kvderevyanko/klicad/hardware/evidence/rev1-preproduction-silkscreen-implementation-2026-08-21/implementation-handoff.md

# Rev.1 pre-production silkscreen implementation handoff

## SCOPE STATUS

`IMPLEMENTED — INDEPENDENT IMPLEMENTATION REVIEW REQUIRED`

The active board now exactly matches the independently reviewed candidate
`hardware/evidence/rev1-preproduction-silkscreen-plan-2026-08-21/20-silkscreen-candidate-b.kicad_pcb`.

## Transaction

- Pre-transaction active SHA-256: `fa4bfbc0db8a9b99583374f5a4f6836f2e5478efc125d0bf91d148ff16ddc1be`.
- Named backup: `01-active-pre-silkscreen-fa4bfbc0.kicad_pcb`.
- Final active SHA-256: `a9fa9493ec7dfbc3f0cfb2c761cb3d6d895543bd6ade34848f83fb86fcffec0c`.
- Final active board is byte-identical to reviewed candidate B (`cmp` PASS and equal SHA-256).
- Exactly 34 board-level `F.SilkS` text objects were added: board `gr_text` count changed from 12 to 46.
- Existing title block and retained Dwgs.User status text were preserved byte-for-byte from the transaction baseline.
- No footprint graphics, footprint origin/rotation, track, via, zone, rule-area, or Edge.Cuts item was changed.

## Critical geometry

All text centres, rotations, sizes, and strokes are exactly those in
`silkscreen-physical-plan.md`. Every new label is at least 0.80 mm high with
0.15-mm stroke; the four high-level orientation labels are 0.90 or 1.00 mm
high. J3 `PIN 1 / M0` remains unchanged.

## Machine gates

- Pre-transaction protected fast contract: PASS.
- Post-transaction protected fast contract: PASS.
- Native KiCad DRC with `--severity-all`: 0 violations, 0 unconnected items.
- Schematic/PCB parity: PASS; 37 PCB footprints and two intentional no-footprint DNP items.
- Full board contract: PASS; 37 footprints, 200 tracks, 58 vias, four zones, two copper layers, 145 x 90 mm.
- Normalized immutability: PASS. The accepted candidate comparison fingerprint is unchanged before/after (`c198408a...c761`); footprint placement/pads, segments, vias, copper zones and fills, antenna keepout, connectivity, and Edge.Cuts are identical.

## Delta and preservation

- Expected DRC delta: none. Observed DRC delta: none.
- Expected copper/placement delta: none. Observed copper/placement delta: none.
- Retained: prior title-block cleanup, prior Dwgs.User cleanup, all completed routing, U3 DBV release, U4 thermal geometry, antenna exclusion, and all footprint positions.
- Deferred: none within this approved transaction.
- Failed: none.

## Next gate

Independent `pcb_reviewer` implementation review. This handoff is a process
status and is not approval.

Evidence: `00-pre-fast-contract.log`, named backup `01-*`,
`02-post-fast-contract.log`, `03-post-drc.json`, `04-post-parity.json`,
`05-post-full-contract.log`, `06-normalized-geometry-delta.json`, and
`07-sha256.log`.
