kvderevyanko/klicad/hardware/evidence/agent-refactor-2026-08-20/agent-context.md

# Active agent context — ESP32 + E220 carrier Rev.1

Audience: `AGENT_FACING`. This is the concise English operational source for agents. Validate mutable geometry and checker counts against the actual files before acting.

## Product boundary

The PCB is a two-layer carrier for a removable 30-pin ESP32 DevKit, one removable EBYTE E220-400T22D or E220-900T22D, and a removable 0.96-inch OLED. The active carrier supply is an externally protected 2S Li-ion pack. Superseded carrier USB-C/TUSB320/eFuse power circuitry must not be restored. The DevKit's own USB-C must remain physically accessible and is subject to the documented Rev.A mutual-use/backfeed constraint.

Factory PCBA installs carrier sockets, battery protection, the TPS62133 power cell, passives, and released carrier circuitry. ESP32 DevKit, E220, and OLED modules are user-installed. R10/R11 are `NO_FOOTPRINT_DNP` OLED pull-up options.

## Rev.1 accessory-power and service policy

`U4` is TI `TLV1117LV33DCYR`, a 5-V-to-3.3-V accessory LDO: U4.3=`5V_SYS`, U4.2/tab=`AUX_3V3`, and U4.1=`GND`. C9 and C10 are the prescribed local 10-uF Murata `GRM21BR61E106KA73` input and output capacitors. The current schematic and the electrical evidence are the controlling records: `hardware/esp32-e220.kicad_sch` (U4/C9/C10) and `hardware/evidence/rev1-expansion-2026-08-20/aux-3v3-electrical-handoff.md`.

`AUX_3V3` has a 300-mA total allocation: OLED at J5 = 100 mA, with J6 and J7 together = 200 mA total, not 200 mA per connector. J5.2, J6.9, J7.2, J7.12, R10.2, and R11.2 are on `AUX_3V3`; R10/R11 remain DNP. `DEVKIT_3V3` is J2.1 only and has no approved external-accessory allocation. Do not power an accessory from `DEVKIT_3V3`.

Normal operation is `POWER_SW ON` with `JP1` closed. For USB service, use `POWER_SW OFF` and `JP1` open when isolation is desired. This does not provide automatic or complete GPIO isolation. With carrier power on, `JP1` open, and the DevKit unpowered, a powered J5/J6/J7 peripheral must not actively drive a GPIO. This is an operating-policy limitation; no extra isolation hardware is authorized in this revision. See the same schematic notes and `aux-3v3-electrical-handoff.md` for the exact statement and U4 thermal/layout constraint.

## Recovered 5V_SYS design allocation

`POWER BUDGET PASS` applies to the recovered simultaneous **project design
allocation**, not to a manufacturer maximum of the unidentified removable
DevKit and not to physical-release approval. The exact ledger is
`500.000 mA` DevKit allocation + `110.000 mA` E220 manufacturer instantaneous
22-dBm maximum + `36.600 mA` unreleased-D2 conservative allocation +
`1.510 mA` U3 static test-condition allocation + `300.100 mA` U4/AUX
allocation convention = `948.210 mA`; 20% engineering margin = `189.642 mA`;
total `5V_SYS` design allocation = `1.137852 A`.

The 100-mA OLED allocation is included once within the 300-mA `AUX_3V3`
allocation; J6/J7 receive the other 200 mA combined. The extra 0.100 mA is
not a claimed U4 loaded-current maximum: TI `TLV1117LV` `SBVS160C`, Rev. C,
states that value as maximum no-load quiescent current. `TPS62133` has a 3.0-A
continuous output rating; this allocation is 37.9284% of it and leaves
1.862148 A continuous-rating headroom. Its 3.6-A minimum static current limit
is specified at VIN=12 V / TA=25°C; it is a separate qualification condition,
not the continuous rating or a 6.0-V guarantee.

At 5.0 V, `Pout=5.689260 W`; at the 85% allocation assumption,
`Pin=6.693247 W`, giving battery current `1.115541 A` / `0.904493 A` /
`0.796815 A` at 6.0 V / 7.4 V / 8.4 V. At the 6.0-V worst allocation, F1
`1812L200/16` retains `0.174459 A` to its 1.29-A 85°C `Ihold`; J4 is 3 A,
Q1 is adequate against its cited 2.6-A at 70°C / VGS=-4.5-V condition, and
the selected J8 JST VH 10-A rating has `8.884459 A` arithmetic difference.
These are design-allocation comparisons; harness, hot-board, ripple, and
transient behavior require prototype validation.

`XFL4020-222MEB` is retained without change. Official Coilcraft
`XFL4020-222ME_` data gives 2.2 uH, 23.50-mOhm maximum DCR, 3.1-A 10%-drop
`Isat`, and 6.0-A 20°C-rise `Irms`. At the DC allocation, its DCR-only loss
is `0.030426 W` and the DC-only gap to 3.1-A `Isat` is `1.962148 A`; peak
inductor current with ripple must be measured or calculated for the actual
board. See `hardware/evidence/rev1-expansion-2026-08-20/5v-sys-budget-ledger.md`.

## Approved electrical topology

Input path:

`BAT_PLUS -> F1 -> BAT_FUSED -> Q1 -> BUCK_IN -> U1 TPS62133 -> 5V_SYS`.

TVS shunt:

`BAT_FUSED -> D3 SMBJ10CA -> GND`.

Q1 DMP3130LQ-7 uses manufacturer pins 1=G, 2=S, 3=D. Approved nets are Q1.1=`Q1_GATE`, Q1.2=`BUCK_IN`, Q1.3=`BAT_FUSED`. Do not infer function from visual pad position.

TPS62133RGT functional map from TI TPS6213x Rev.F Table 6-1:

| Pins | Function | Approved net/intent |
| --- | --- | --- |
| 1, 2, 3 | SW | `BUCK_SW` to L1, short F.Cu only |
| 4 | PG | NC in the approved design |
| 5 | FB | GND for fixed output |
| 6 | AGND | local common ground/EP |
| 7 | FSW | `5V_SYS`, logic-high frequency selection; low-current configuration trace |
| 8 | DEF | GND output selection |
| 9 | SS/TR | `SS_TR` to C4; mandatory short control connection |
| 10 | AVIN | `BUCK_IN` with local C2 bypass |
| 11, 12 | PVIN | `BUCK_IN` with local C1 high-di/dt loop |
| 13 | EN | `BUCK_IN` |
| 14 | VOS | `5V_SYS` Kelvin sense at/near C3 output node, not a power branch |
| 15, 16 | PGND | local common ground/EP |
| EP | exposed pad | GND/thermal connection |

No schematic change is currently required for the TPS62133 cell.

## Module interfaces

E220 mapping: GPIO17/TX2 -> E220 RXD; GPIO16/RX2 <- E220 TXD; GPIO25 -> M0; GPIO26 -> M1; GPIO27 <- AUX. M0/M1 have local 10-kOhm pull-downs. E220 VCC uses local 10-uF + 100-nF decoupling. Preserve SMA access and RF separation.

OLED mapping: J5.1=GND, J5.2=`AUX_3V3`, J5.3=GPIO22/SCL, J5.4=GPIO21/SDA. R10/R11 4.7-kOhm pull-ups to `AUX_3V3` are DNP/no-footprint. OLED final mechanical datum remains unresolved.

WS2812/AHCT: U3 SN74AHCT1G125 is approved. D2 remains `PLACEMENT_CANDIDATE_NOT_RELEASED`; do not production-approve its footprint or route final D2-dependent connections unless explicitly released.

## Mechanical and PCB baseline

Board outline: 145 x 90 mm. Planning stack: two layers, 1-oz outer copper assumption pending fabrication confirmation. ESP32, E220, OLED, and J4 locations are protected from casual movement. Preserve ESP32 antenna keepout, DevKit USB-C access, E220 SMA access, and module-removal clearance.

Planning rules:

* SIGNAL: preferred 0.25 mm, 0.20 mm minimum for tight escape, 0.20 mm clearance, 0.60/0.30-mm via.
* POWER: BAT_PLUS, BAT_FUSED, BUCK_IN, and main 5V_SYS preferred 1.0 mm; justified local 5V_SYS branches may use 0.8 mm.
* BUCK_SW: short local F.Cu, no via, minimum practical copper, 0.70 mm accepted where 0.80 mm violates actual clearance.

## Current physical state

The active board `hardware/esp32-e220.kicad_pcb` is the accepted controlled-routing physical state of record. Its input protection, TPS62133 buck implementation, and post-C3 `5V_SYS` distribution were independently reviewed and accepted as physical checkpoints; this is not a production release or a substitute for the final independent PCB review.

The active board contains the accepted buck and 5V copper, the bounded B.Cu GND plane, and the local F.Cu buck GND zone. Retain the VOS Kelvin connection at the C3 output node and the FSW configuration connection. The completed power endpoints are ESP32 VIN, E220 VCC with C5/C6 bypass, and U3/C7 power. Only D2.1 remains on the `5V_SYS` deferred list because D2 is `PLACEMENT_CANDIDATE_NOT_RELEASED`; no D2-dependent copper is released.

The active PCB contains a **partial, blocked** Rev.1 expansion transaction: J8/JP1/BAT_SENSE/U4/C9/C10 are present and their changed existing-pad parity is applied, but J6/J7 plus all authorized M3/strain-relief holes are not retained. U4/C9/C10 ground returns and AUX_3V3 endpoint completion remain mandatory airwires. This is not physical approval; see `hardware/evidence/rev1-expansion-2026-08-20/physical-handoff.md`. No schematic owner may edit the active board.

Remaining signal, OLED, UART, GPIO, RF-interface, and test-point connections are unrouted. OLED mechanics remain pending. The active board also intentionally retains the deferred input/test-point airwires `/BAT_PLUS` TP1-to-track and `/BUCK_IN` R2.1-to-track-to-TP3; do not claim that all global electrical airwires are gone and do not repair these outside this scope.

Historical candidate facts are retained only as history: `hardware/esp32-e220-assistant-buck-candidate.kicad_pcb` is an unrouted 0-track/0-via/0-zone placement candidate, not routing authority or a reviewer-approved replacement. `hardware/make_assistant_buck_candidate.py` reproduces that separate candidate without overwriting the active board.

## Deferred items

* OLED mechanical datum/final short connector fanout: pending.
* D2 WS2812 footprint remains `PLACEMENT_CANDIDATE_NOT_RELEASED`; D2-dependent routing is pending.
* All non-power signal routing and the final OLED mechanical integration: pending.
* U4 `AUX_3V3` physical footprint verification, thermal copper/vias, accessory connector placement, and all associated PCB parity/DRC work: pending with `pcb_layout_dfm` after electrical review.
* Prototype validation remains required for DevKit burst/startup current, external-device inrush and capacitance, U4 temperature at the authorized load, TPS62133/F1/Q1 transients, and L1 peak current; the `POWER BUDGET PASS` design allocation is not a prototype result.
* The active PCB is not a production release.

## Primary operational files

* `hardware/esp32-e220.kicad_sch` — approved electrical schematic.
* `hardware/esp32-e220.kicad_pcb` — active controlled-routing physical state.
* `hardware/generate_esp32_e220.py` — reproducible schematic source.
* `hardware/generate_stage7_footprints.py` — active footprint-library source.
* `hardware/generate_stage8_placement.py` — pre-routing candidate generator only; requires an explicit non-active `PLACEMENT_OUTPUT` and never overwrites the active board.
* `hardware/make_assistant_buck_candidate.py` — historical feasibility helper for the separate buck candidate.
* `hardware/rework_buck_local.py` — obsolete failed experiment; not routing authority.
* `hardware/route_5v_distribution.py` — accepted completed-stage helper; requires an explicit board path and stops with `STAGE ALREADY APPLIED` before reapplying accepted copper.
* `hardware/esp32-e220.kicad_pcb` — active routed PCB physical state record.
* `hardware/check_schematic_pcb_sync.py` — approved machine sync gate.
* `hardware/esp32-e220-power-routing-report.md` — English detailed routing checkpoint evidence.
* `hardware/esp32-e220.pretty/README.md` — English footprint-library evidence.

## Required validation

Use native KiCad ERC/DRC and the project sync checker. Report DRC geometry separately from expected out-of-scope unconnected items. Never alter connectivity merely to silence a checker; classify representation differences versus real mismatches. Final electrical and physical acceptance belongs only to `pcb_reviewer`.
