kvderevyanko/klicad/hardware/releases/rev1-q1-footprint-correction-2026-09-11/fabrication/DRILL_REPORT.txt

Drill report for esp32-e220.kicad_pcb
Created on 2026-09-11T11:37:57

Copper Layer Stackup:
    =============================================================
    L1 :  F.Cu                      front
    L2 :  B.Cu                      back

Drill file 'esp32-e220-PTH.drl' contains
    plated through holes:
    =============================================================
    T1  0.300mm  0.0118"  (58 holes))
    T2  1.000mm  0.0394"  (20 holes))
    T3  1.040mm  0.0409"  (41 holes))

    Total plated holes count 119

Drill file 'esp32-e220-NPTH.drl' contains
    unplated through holes:
    =============================================================
    T1  3.200mm  0.1260"  (3 holes))

    Total unplated holes count 3
