kvderevyanko/klicad/docs/open-questions.md

# Вопросы первой статьи Rev.1

Электрическая архитектура, размещение, трассировка и возвратные пути Rev.1 завершены. Этот список не разрешает изменение платы без отдельной согласованной стадии.

## OLED

Розетка J5 и её электрические цепи завершены. Конкретный OLED остаётся механическим риском первой статьи: подтвердить габариты корпуса, высоту, отверстия, доступность разъёма и зазоры. Не вводить на фабричном шелкографии непроверенный точный контур дисплея.

## Корпус и жгут

- Крепёж платы: **отложен до корпуса / Rev.2**. На Rev.1 не добавлять произвольные монтажные отверстия без датумов корпуса.
- Разгрузка аккумуляторного кабеля: **ответственность корпуса / жгута в Rev.1**.
- Проверить доступ к J4, J8, JP1, USB-C ESP32, SMA E220, J5, J6, J9 и TP1…TP5 с реальными разъёмами и инструментом.

## Проверки первого образца

- переходные процессы батареи, F1/D3/Q1 и TPS62133;
- температура U1, L1, Q1, F1, D3 и U4 при OLED-нагрузке;
- фактический ток OLED и внешней цепи до трёх WS2812B-V5;
- работа E220 с согласованной 400- или 900-МГц антенной;
- сопряжение розеток с фактическими ESP32 DevKit, E220 и OLED;
- кнопки J6 и пользовательский RGB J9;
- технологические возможности сборщика для EP U1, U4 SOT-223 и DBV U3.

## Политика выпуска

Rev.1 имеет завершённую связность, но пока не является производственным выпуском. Gerber, сверловка, производственный BOM и CPL создаются только отдельной задачей после финального предсерийного ревью.
