kvderevyanko/klicad/hardware/evidence/preexisting-esp32-e220-artifacts/esp32-e220-gate.pdf

1 | 2 | 3 | 4 | 5 | 6
1 | 2 | 3 | 4 | 5 | 6

AB

C

D

AB

C

D Date:

Size: A4 | Rev:
KiCad E.D.A. 10.0.5 | Id: 1/1

## Title: ESP32 E220 LoRa Receiver — Stage 5 modular carrier

File: esp32-e220.kicad_sch

Sheet: /

2 R5

2 C1

# #FLG02 PWR_FLAG

# #FLG01 PWR_FLAG

# 2 D1 MMSD4148T1G

2 R7

2 C3

1

2

3

4

5

6

7

8 U2

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
15 | J1 DEVKIT_LEFT (USB-C | toward antenna)

2 R6

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
15 | J2 DEVKIT_RIGHT (USB-C | toward antenna) A1

A4

A5

A6

A7

A8

A9

## A12 B1B4B5B6B7B8B9 B12

SH1

# SH2 J4 USB4105-GF-A

1

2

3

4

5

6

7 J3

E220-T22D SOCKET — | FIT | 400T22D OR 900T22D

1

2 C6 GRM188R71C104KA01D 100nF 16V X7R

1

2 C5 GRM188R61A106MAAL 10uF 10V X5R

1

2 R8

10k 1% M0 reset pull-down

1

2 R9

10k 1% M1 reset pull-down

1

2

3

4

5 U3

SN74AHCT1G125DBVR

1

2 C7 GRM188R71C104KA01D 100nF 16V X7R

2 R1

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
12 U1

# #FLG03 PWR_FLAG 1

OLED_SDA OLED_SCL CC2

VBUS_DET USB_DP_NC

E220_RXD USB_DM_NC

CC1

E220_TXD

E220_M0
E220_M1
E220_RXD

E220_M0

VBUS_PRE GND

GND

VBUS_PRE USB_DP_NC

CC1

VBUS_PRE GND

E220_TXD WS2812_DATA_3V3 GND

5V_SYS

TUSB_VDD

5V_SYS

# 5V_SYS GND

WS2812_DATA_3V3 GND WS2812_DIN

GND

GND

# 5V_SYS GND

5V_SYS

E220_AUX

5V_SYS GND

E220_M0 | E220_M1 CC2 GND
GND | GND OVLO

OUT1

5V_SYS GND

DVDT EFUSE_EN

GND

# 5V_SYS USB_DM_NC

VBUS_PRE

VBUS_PRE GND

GND

GND | QBASE

# VBUS_PRE GND

TUSB_VDD

E220_M1

# E220_AUX GND QBASE

GND

5V_SYS

ILM
OVLO

TUSB320 UFP/GPIO: PORT=GND, ADDR=NC, EN_N=GND. OUT1/Q1 gates TPS259630: Default/detach OFF; Medium/High ON.

GPIO4 -> SN74AHCT1G125DBVR (OE=GND, | 5V) | -> WS2812B-V5 DIN. No WS2812 footprint assigned at schematic stage.

USB4105-GF-A: all A/B VBUS, GND and shell contacts are explicit; D+/D- are local NC nets, SBU pins NC, no ESP USB connection.

Stage 5 — main board only. DevKit USB-C programming and main-board USB-C power are mutually exclusive (approved Rev A policy).

No bare ESP32, 3V3 buck, EN/BOOT or programming circuit on this PCB. J1/J2 are the verified removable DevKit sockets.

J3 is universal E220-T22D interface: fit one E220-400T22D OR E220-900T22D. No socket/footprint is selected.

E220 M0/M1 use 10k pull-downs to GND (PROJECT DESIGN CHOICE): reset mode M1/M0=00. AUX is input-only, no pull-down.

OLED: GPIO21/SDA and GPIO22/SCL are signal-only reservations; OLED VCC and I2C pull-ups are NC/DNP in Rev A.

2 U1

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
12 #FLG03 PWR_FLAG

R1

2 C1

# 2 #FLG02 PWR_FLAG #FLG01 PWR_FLAG

# D1 MMSD4148T1G

2 R5

2 | R6

J3

E220-T22D SOCKET — | FIT | 400T22D OR 900T22D

1

2

3

4

5

6
7 | C6 GRM188R71C104KA01D 100nF 16V X7R

1

2 C5 GRM188R61A106MAAL 10uF 10V X5R

1

2 | R8

10k 1% M0 reset pull-down

1

2 | R9

10k 1% M1 reset pull-down

1

2 | U3

SN74AHCT1G125DBVR

1

2

3

4
5 | C7 GRM188R71C104KA01D 100nF 16V X7R

1

2
