kvderevyanko/klicad/hardware/evidence/preexisting-esp32-e220-artifacts/esp32-e220-oled-final.pdf

1 | 2 | 3 | 4 | 5 | 6
1 | 2 | 3 | 4 | 5 | 6

AB

C

D

AB

C

File: | esp32-e220.kicad_sch | D Date:
| | | DEVKIT_3V3 GND
KiCad E.D.A. 10.0.5 | Id: 1/1
Size: | A4 | Rev:

## Title: ESP32 E220 LoRa Receiver — Rev.1 protected 2S battery carrier

Sheet: / | 1

# TP2 GND

TP7

E220_M1

1

2 R9

10k 1% M1 reset pull-down

1

2 R1

100k 1% (Q1 gate pull-down) 1

2 D3

SMBJ10CA (bidirectional TVS) 1

2 R2

1M 1% (Q1 gate-source)

# #FLG04 PWR_FLAG

# #FLG03 PWR_FLAG

1

2

3

4

5 U3

SN74AHCT1G125DBVR

# #FLG05 PWR_FLAG

1

2 F1

1812L200/16 (2A hold PPTC) | TP8

E220_AUX

1

2 J4 PROTECTED 2S LI-ION INPUT ONLY 6...8.4V

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
EP | U1
TPS62133RGT | (5V | / 3A BUCK) 1

2

3 Q1 DMP3130LQ-7 | (reverse-polarity) | 1

2 C4 GRM1885C1H332JA01D 3.3nF 50V C0G (SS/TR)

# #FLG02 PWR_FLAG

# #FLG01 PWR_FLAG

1

2 C2 GRM188R71C104KA01D 100nF 16V X7R (AVIN) 1

2 C1 GRM21BR61E106KA73 10uF 25V X5R (BUCK IN)

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
15 | J1 DEVKIT_LEFT (USB-C | toward antenna) | 1

2

3

4

5

6

7 J3

E220-T22D SOCKET — | FIT | 400T22D OR 900T22D

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
15 | J2 DEVKIT_RIGHT | (USB-C | toward antenna) | TP3 BUCK_IN

1

2 L1

XFL4020-222MEB 2.2uH

1

2 C6 GRM188R71C104KA01D 100nF 16V X7R

TP1 BAT_PLUS

TP6

E220_M0

1

2 C7 GRM188R71C104KA01D 100nF 16V X7R

1

2 R8

10k 1% M0 reset pull-down

TP9

E220_RXD

E220_VCC

E220_TXD

TP4

5V_SYS

1

2 R10 DNP 4.7k 1% OLED SDA pull-up to 3V3

1

2 C5 GRM188R61A106MAAL 10uF 10V X5R

1

2 C3 GRM21BR61A226ME44 22uF 10V X5R (BUCK OUT) BUCK_IN

BUCK_IN

GND

BUCK_IN

SS_TR

BUCK_IN

GND

GND

5V_SYS

5V_SYS

E220_AUX BUCK_IN

BUCK_IN
GND
BUCK_IN | SS_TR

GND

BUCK_SW

BUCK_SW

BUCK_SW

WS2812_DATA_3V3 DEVKIT_3V3 | BUCK_IN
Q1_GATE | OLED_SDA OLED_SDA 5V_SYS DEVKIT_3V3
E220_RXD | WS2812_DIN

5V_SYS WS2812_DATA_3V3 GND

GND WS2812_DIN

OLED_SCL 5V_SYS | OLED_SCL DEVKIT_3V3
5V_SYS | GND

GND

GND

GND
GND

5V_SYS BUCK_IN

E220_M1 GND

GND

E220_M1 Q1_GATE | BUCK_IN
GND | Q1_GATE DEVKIT_3V3 | BAT_PLUS BAT_PLUS GND

BAT_PLUS BAT_FUSED

BAT_PLUS | OLED_SDA OLED_SCL E220_TXD

GND

E220_M0
E220_M1
E220_RXD

GND

5V_SYS

5V_SYS BUCK_SW

5V_SYS BAT_FUSED

E220_M0 GND | GND

E220_AUX
5V_SYS GND

5V_SYS

E220_M0 BAT_FUSED

E220_M0

E220_M1

E220_AUX

E220_TXD

GND

GND

# 5V_SYS GND

5V_SYS | GND

E220_RXD

TP1 BAT_PLUS, TP2 GND, TP3 BUCK_IN, TP4 5V_SYS, TP5 E220_VCC(5V_SYS), TP6 M0, TP7 M1, TP8 AUX, TP9 RXD, TP10 TXD.

GPIO4 -> SN74AHCT1G125DBVR (OE=GND, 5V) -> WS2812B-V5 DIN. No PCB footprint/layout work is included.

TPS62133: PVIN/AVIN/EN=BUCK_IN, SW1-3 -> L1 2.2uH -> 5V_SYS, VOS/FSW=5V_SYS, FB/DEF/grounds/EP=GND, SS/TR=C4 to GND; PG NC.

Rev.1 active input: externally protected 2S 18650 pack + external BMS only. J4 is BAT+/BAT- 6.0...8.4V; no midpoint, charger or USB-C input.

D3 SMBJ10CA is a bidirectional input transient clamp at BAT_FUSED. No on-board charger/BMS is duplicated; no main-board switch is fitted in Rev.1.

Rev.1 policy: disconnect battery or turn its external BMS output off before connecting the removable DevKit USB-C to a computer for programming.

J3 is universal E220-T22D: fit one E220-400T22D OR E220-900T22D. M0/M1 10k pulldowns. J5 is removable SSD1306 0.96 I2C, 1 GND/2 3V3/3 SCL/4 SDA.

OLED VCC is DEVKIT_3V3 only. R10/R11 optional DNP 4.7k pull-ups to 3V3; fit only after checking module pull-ups. No 5V OLED power or pull-up.

BAT+ -> F1 1812L200/16 -> BAT_FUSED -> Q1 DMP3130LQ-7 reverse-polarity MOSFET -> BUCK_IN -> U1 TPS62133RGT -> 5V_SYS.

L1

XFL4020-222MEB 2.2uH

1
2 | C3 GRM21BR61A226ME44 22uF 10V X5R (BUCK OUT) 1
2 | TP1 BAT_PLUS C6 GRM188R71C104KA01D 100nF 16V X7R

1
2 | TP6

# E220_M0 R8

10k 1% M0 reset pull-down

1

2 C5 GRM188R61A106MAAL 10uF 10V X5R

1
2 | TP2 GND

TP7

# E220_M1 R9

10k 1% M1 reset pull-down

1
2 R1

100k 1% (Q1 gate pull-down) 1

2 D3

SMBJ10CA (bidirectional TVS) 1

2 | R2

1M 1% (Q1 gate-source) 1
2 #FLG04 PWR_FLAG

# #FLG03 PWR_FLAG

# #FLG05 PWR_FLAG

F1

1812L200/16 (2A hold PPTC) 1

2 J4 PROTECTED 2S LI-ION INPUT ONLY 6...8.4V

1

2 | Q1 DMP3130LQ-7 | (reverse-polarity) 1

2
3 #FLG02 PWR_FLAG

# #FLG01 PWR_FLAG

J3

E220-T22D SOCKET — | FIT | 400T22D OR 900T22D

1

2

3

4

5

6
7 J2 DEVKIT_RIGHT | (USB-C | toward antenna) 1

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
15 | C1 GRM21BR61E106KA73 10uF 25V X5R (BUCK IN) 1
2 | C2 GRM188R71C104KA01D 100nF 16V X7R (AVIN) 1
2 | C4 GRM1885C1H332JA01D 3.3nF 50V C0G (SS/TR) 1

2 U1
TPS62133RGT | (5V | / 3A BUCK) 1

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
SN74AHCT1G125DBVR

1

2

3

4

# 5 R10 DNP 4.7k 1% OLED SDA pull-up to 3V3

1

2 TP4

5V_SYS

E220_TXD

E220_VCC
TP9

E220_RXD

C7 GRM188R71C104KA01D 100nF 16V X7R

1

2
