kvderevyanko/klicad/docs/footprint-mechanical-review.md

# Проверка посадочных мест и механики

Назначение: русскоязычный отчёт для человека. Англоязычное описание библиотеки для агентов находится в `hardware/esp32-e220.pretty/README.md`.

## Граница проверки

Библиотека `hardware/esp32-e220.pretty` создаётся воспроизводимым скриптом `hardware/generate_stage7_footprints.py`. Наличие посадочного места в библиотеке не означает автоматического разрешения на производство. Электрическая схема при этой проверке не изменялась.

Для каждого элемента различаются:

- подтверждённый изготовителем корпус и нумерация выводов;
- рекомендуемый рисунок площадок;
- проектная площадка, построенная по номинальным правилам IPC;
- пользовательский механический шаблон;
- кандидат, не разрешённый для изготовления.

## J4 — вход аккумулятора

Выбран JST `B2B-XH-A`:

- два вывода;
- шаг 2,500 мм;
- сверление 1,000 мм;
- медная площадка проекта 1,70×2,00 мм;
- ответный корпус `XHP-2`;
- контакт `SXH-001T-P0.6`.

Перед выпуском проверить доступность деталей, сечение провода, изгиб жгута и разгрузку натяжения.

## Розетки Samtec SSW

Выбраны:

- J1/J2: `SSW-115-02-G-S`;
- J3: `SSW-107-02-G-S`;
- J5: `SSW-104-02-G-S`.

Официальный чертёж Samtec подтверждает шаг 2,540 мм и сверление 1,040 мм. Диаметр меди 1,70 мм является проектным выбором, поскольку в чертеже не задан рекомендуемый диаметр медной площадки. Его должен подтвердить выбранный сборщик.

J6 (`BUTTONS`, 1×6) и J9 (`J_RGB`, 1×3) используют отдельные проектные
однорядные посадочные места `PinHeader_1x06_P2.54mm_Vertical` и
`PinHeader_1x03_P2.54mm_Vertical`. Для них приняты шаг 2,540 мм, сверление
1,000 мм и медь 1,70 мм. Это общие ремонтопригодные точки под пользовательский
штыревой разъём или прямую пайку провода; обе позиции имеют `DNP=YES` и не
считаются заводскими розетками Samtec.

## Модуль ESP32 DevKit

Подтверждены:

- две однорядные группы по 15 выводов;
- шаг 2,540 мм;
- расстояние между центрами рядов 25,400 мм.

Габарит 28×51 мм получен от пользователя и не привязан точным чертежом к выводам, USB-C и антенне. Поэтому `ESP32_DevKit_30pin_Socket_2x15_MechanicalTemplate` является консервативным шаблоном. Он годится для предварительного размещения, но не доказывает точную антенную область или корпус.

Обязательны:

- край платы со стороны антенны;
- область без меди и компонентов;
- прямой доступ к USB-C;
- место для вертикального извлечения модуля.

## E220-400T22D / E220-900T22D

Официальный общий чертёж EBYTE, STEP и библиотека E220-900T22D подтверждают:

- габарит 21×36 мм;
- семь выводов с шагом 2,540 мм;
- общую сторону SMA;
- общие ориентиры крепёжных отверстий.

Шаблон `E220_T22D_Socket_400_900` представляет розетку несущей платы, а не паяные площадки самого модуля. Точки отверстий 8…10 показываются как механические ориентиры и не создаются как контакты либо NPTH.

До серийной сборки требуется примерить фактический модуль к `SSW-107-02-G-S`, проверить глубину входа выводов, нижние элементы, высоту и доступ SMA. Антенны диапазонов 400 и 900 МГц не взаимозаменяемы.

## Дисплей OLED

Шаблон `OLED_0p96_4pin_MechanicalTemplate_PENDING_DATUM` хранит только подтверждённые пользовательские размеры:

- плата 26,000×26,000 мм;
- шаг разъёма 2,540 мм;
- расстояния крепёжных отверстий X=21,740 мм и Y=22,000 мм;
- координаты выводов GND/VCC/SCL/SDA по X от левого края 9,190/11,730/14,270/16,810 мм.

Не подтверждены:

- координата ряда разъёма по Y;
- окончательный диаметр отверстий;
- положение отверстий относительно краёв и разъёма по полному исходному чертежу;
- габариты стекла, шлейфа, нижних элементов и выреза.

Поэтому шаблон не создаёт окончательные крепёжные отверстия и не разрешён для производственного выпуска.

## TPS62133RGT

Посадочное место `TI_TPS62133RGT_RGT0016C` основано на официальном чертеже TI RGT0016C:

- 16 периферийных площадок 0,600×0,240 мм;
- расстояние между центрами противоположных рядов 2,800 мм;
- медная открытая площадка EP 1,680×1,680 мм;
- апертура пасты 1,550×1,550 мм, около 85 % площади.

Встроенный массив переходных отверстий намеренно отсутствует. Обычные внешние тепловые/заземляющие отверстия выбираются после размещения так, чтобы не требовать дорогого заполнения и закрытия и не вызывать чрезмерное вытягивание припоя.

## Дроссель Coilcraft XFL4020-222MEB

Посадочное место повторяет рекомендуемую изготовителем геометрию корпуса XFL4020. При размещении площадка 1 должна смотреть к выводам SW U1, а площадка 2 — к C3. Требуется свободная область вокруг переключающего узла и удаление от антенн ESP32/E220.

## DMP3130LQ-7

Используется корпус SOT-23 по официальному чертежу Diodes Inc. Нумерация 1=G, 2=S, 3=D обязательна; нельзя выводить назначение из зрительного положения площадок после поворота.

## F1, D3 и пассивные элементы

- `1812L200/16` соответствует корпусу 4532 и официальному габариту Littelfuse; медь является проектной номинальной площадкой IPC.
- `SMBJ10CA` соответствует DO-214AA; медь является проектной номинальной площадкой IPC.
- корпуса Murata GRM21/GRM188 соответствуют выбранным размерам изготовителя; конкретная медь должна быть подтверждена сборщиком.
- резисторы используют проектную номинальную геометрию 0603, пока не выбран окончательный MPN для каждой позиции.

Эти вопросы относятся к закупке и DFM, а не разрешают менять номиналы или схему.

## Буфер SN74AHCT1G125

`TI_SN74AHCT1G125DBVR_SOT23-5` является рабочим посадочным местом корпуса DBV/SOT-23-5 выбранного U3. Перед производством проверить точный MPN, метку вывода 1, ориентацию и доступ развязывающего конденсатора C7.

## WS2812B-V5

Бортовой D2 и `WorldSemi_WS2812B-V5_PLACEMENT_CANDIDATE_NOT_RELEASED`
удалены из действующей воспроизводимой библиотеки. На несущей плате остаётся
только J9 для внешней RGB-цепочки; геометрия самих пикселей не является частью
этой платы.

## Контрольные точки

`TestPoint_THT_1p0mm_PROTOTYPE` сохраняется только для TP1…TP5 и имеет
сверление 1,0 мм. TP6…TP10 удалены. Для серийной платы требуется выбрать
изделие, подтвердить доступ щупа и согласовать технологию со сборщиком.

## Предварительное размещение

Текущий проект использует:

- контур 145×90 мм;
- ESP32 28×51 мм;
- E220 21×36 мм;
- OLED 26×26 мм с резервом 36×36 мм;
- не менее 5 мм между физическими габаритами съёмных модулей;
- дополнительные зазоры для извлечения, USB, SMA, инструмента и крепежа.

Этот контур удобен для Rev.1, но не является минимально возможным. Уменьшение допускается только после принятой силовой ячейки, трассировки, земли и проверки корпуса.

## Границы производственного разрешения

Перед выпуском закрыть:

1. недостающие размеры OLED;
2. сопряжение E220 и ESP32 с фактическими розетками;
3. тепловое решение TPS62133;
4. подтверждение сборщика для проектных площадок IPC, J6/J9 и колец Samtec;
5. доступ к USB-C, SMA, J4, J6, J9 и TP1…TP5;
6. окончательные зазоры корпуса и жгута.

## Проверка воспроизводимости

Скрипт `hardware/generate_stage7_footprints.py` должен воспроизводить библиотеку без ручного расхождения. После изменения каждого посадочного места необходимо проверить чтение KiCad, нумерацию площадок, слои, пасту, маску, контур корпуса и дворик.
