kvderevyanko/klicad/hardware/evidence/preexisting-esp32-e220-artifacts/esp32-e220-schematic.txt

                  1                                          2                                        3                                         4                                         5                                    6                                         7                         8

    POWER INPUT: EXTERNALLY PROTECTED 2S LI-ION | 6.0 ... 8.4 V | NO CHARGER ON CARRIER PCB

    WARNING: TURN OFF / DISCONNECT BATTERY POWER BEFORE CONNECTING ESP32 DEVKIT USB-C TO A COMPUTER.

    ESP32 DEVKIT, E220 AND OLED ARE USER-INSTALLED MODULES.
A                                                                                                                                                                                                                                                                                                                 A
    Inter-block links use net labels. Local wires show the active power, bypass and interface support networks.

    C. REMOVABLE ESP32 DEVKIT
    30 PIN / 2x15     |      USB-C + CH340C ON MODULE
    LEFT HEADER: J1                                      RIGHT HEADER: J2

                                                                                                                       D. E220-T22D UNIVERSAL SOCKET                                                    F. WS2812 STATUS LED
                                                                                                                       E220-400T22D / E220-900T22D — user-installed module                              GPIO4 -> AHCT buffer -> DIN

                                              1
                                            5V_SYS                                  1
                                                                                  DEVKIT_3V3
                                              2
                                            GND                                     2
                                                                                  GND
B                                                                                                                                                                                                                                                                                                                 B
                                              3                                     3
                                              4                                     4
                                              5                                     5
                                                                                  WS2812_DATA_3V3
                                              6
                                            E220_AUX                                6
                                                                                  E220_TXD
                                              7
                                            E220_M1                                 7
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
                                                                                                          GND
                                                                                                                  C4
                                                                                                                                             2
                                                                                                                                            GND
                                                                                                                                                     C3                                                               J5: 1 GND | 2 DEVKIT_3V3 | 3 GPIO22/SCL | 4 GPIO21/SDA | R10/R11 4.7k DNP

    J4 BAT+ -> F1 2A PPTC -> D3 SMBJ10CA -> Q1 DMP3130LQ-7 -> BUCK_IN
                                                                 U1 TPS62133RGT: C1 10uF input | C2 100nF AVIN | C4 3.3nF SS | L1 2.2uH | C3 22uF output
                    DEVKIT_3V3

E                                                                                                                                                                                                                                                                                                                 E

                                                                                                                                                                                                                                               Sheet: /
                                                                                                                                                                                                                                               File: esp32-e220.kicad_sch
                                                                                                                                                                                                                                               Title: ESP32 E220 LoRa Receiver — Rev.1 protected 2S battery carrier
                                                                                                                                                                                                                                               Size: A3           Date:                            Rev:
                                                                                                                                                                                                                                               KiCad E.D.A. 10.0.5                                 Id: 1/1
F                 1                                          2                                        3                                         4                                         5                                    6                                         7                         8              F
