kvderevyanko/klicad/hardware/releases/rev1/diagnostics/Drill_Map_NPTH.pdf

Drill Map:
3.200mm / 0.1260" (3 holes) (not plated)
