kvderevyanko/klicad/hardware/evidence/buck-and-5v-checkpoints-2026-08-18/5v-review-top.png

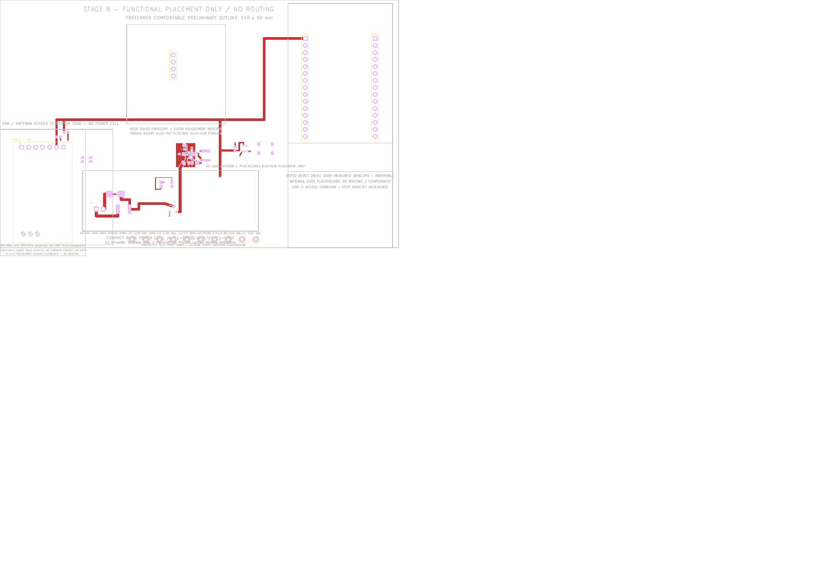
hardware/evidence/buck-and-5v-checkpoints-2026-08-18/5v-review-top.png
