kvderevyanko/klicad/hardware/evidence/buck-and-5v-checkpoints-2026-08-18/assistant-buck-temp-proof.png

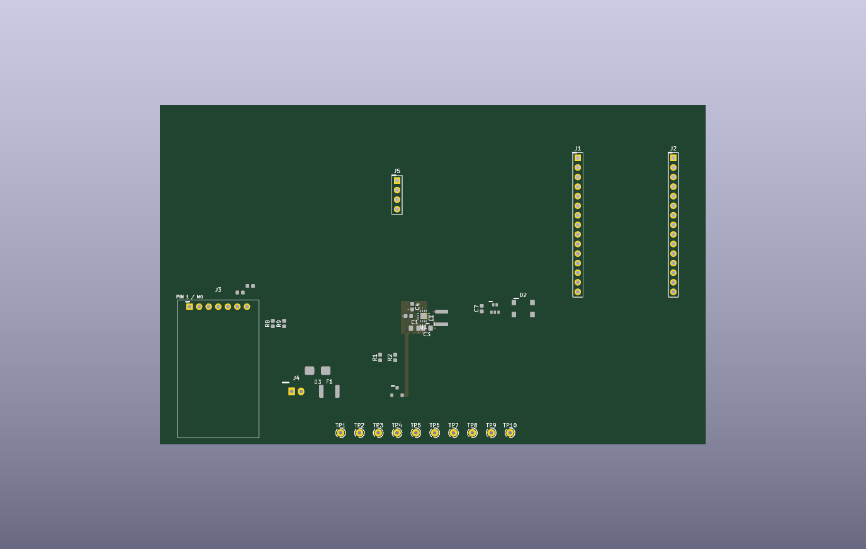
hardware/evidence/buck-and-5v-checkpoints-2026-08-18/assistant-buck-temp-proof.png
