kvderevyanko/klicad/hardware/evidence/buck-and-5v-checkpoints-2026-08-18/buck-review-top-crop.png

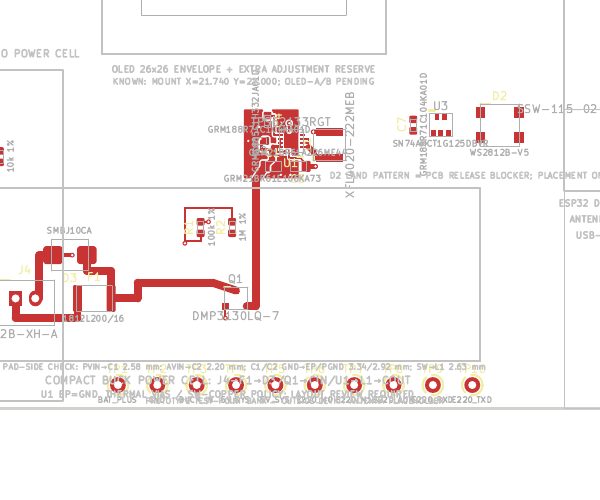
hardware/evidence/buck-and-5v-checkpoints-2026-08-18/buck-review-top-crop.png
