kvderevyanko/klicad/hardware/evidence/preexisting-esp32-e220-artifacts/esp32-e220-pregate.png

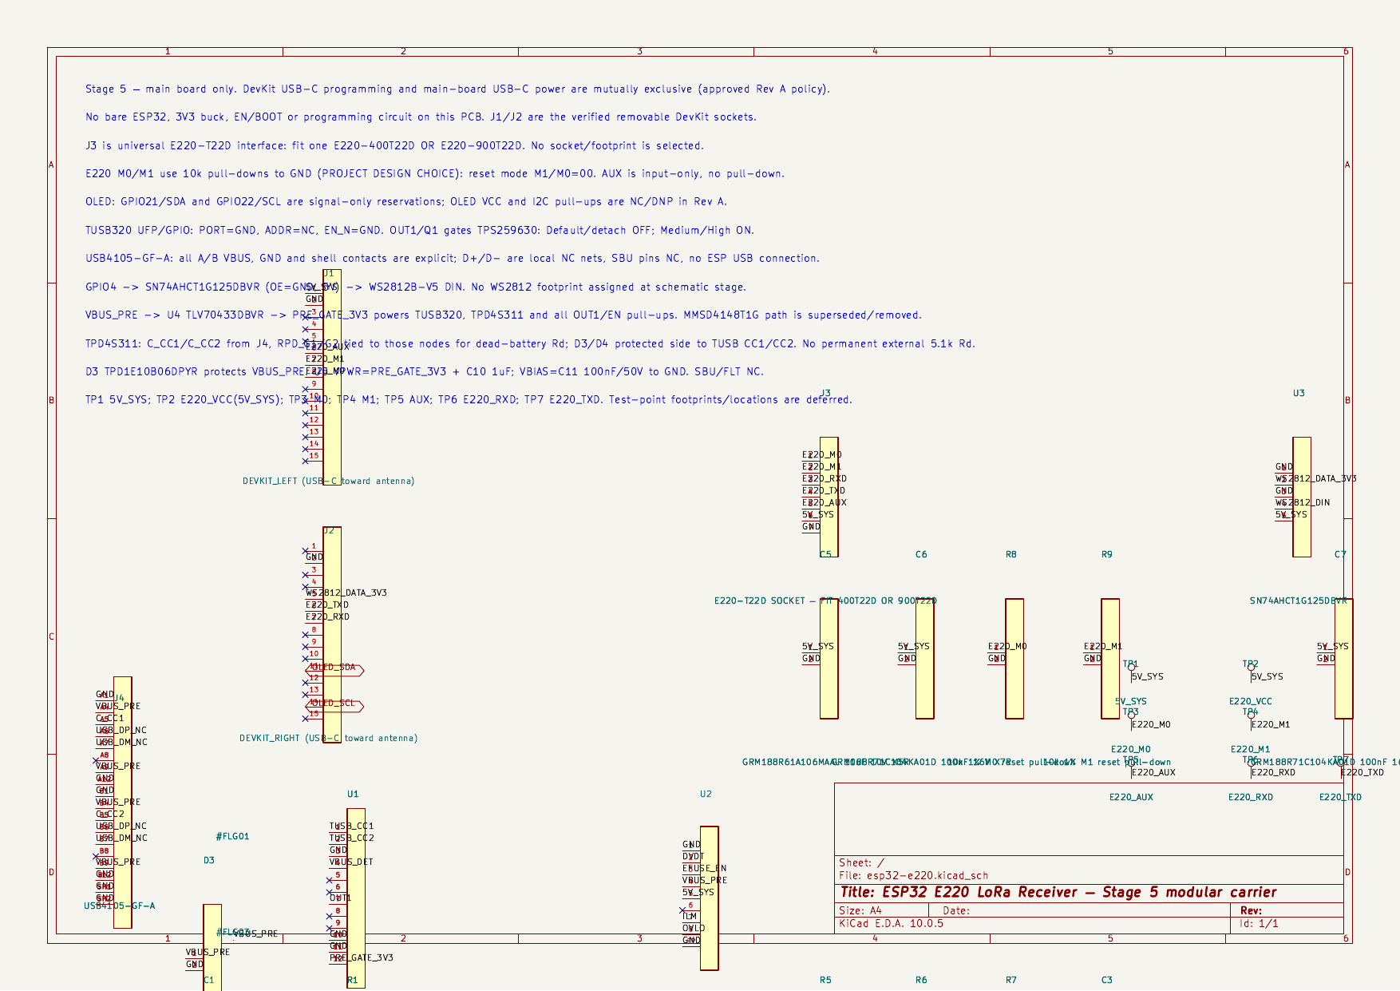
hardware/evidence/preexisting-esp32-e220-artifacts/esp32-e220-pregate.png
