kvderevyanko/klicad/hardware/evidence/preexisting-esp32-e220-artifacts/esp32-e220-rev1.png

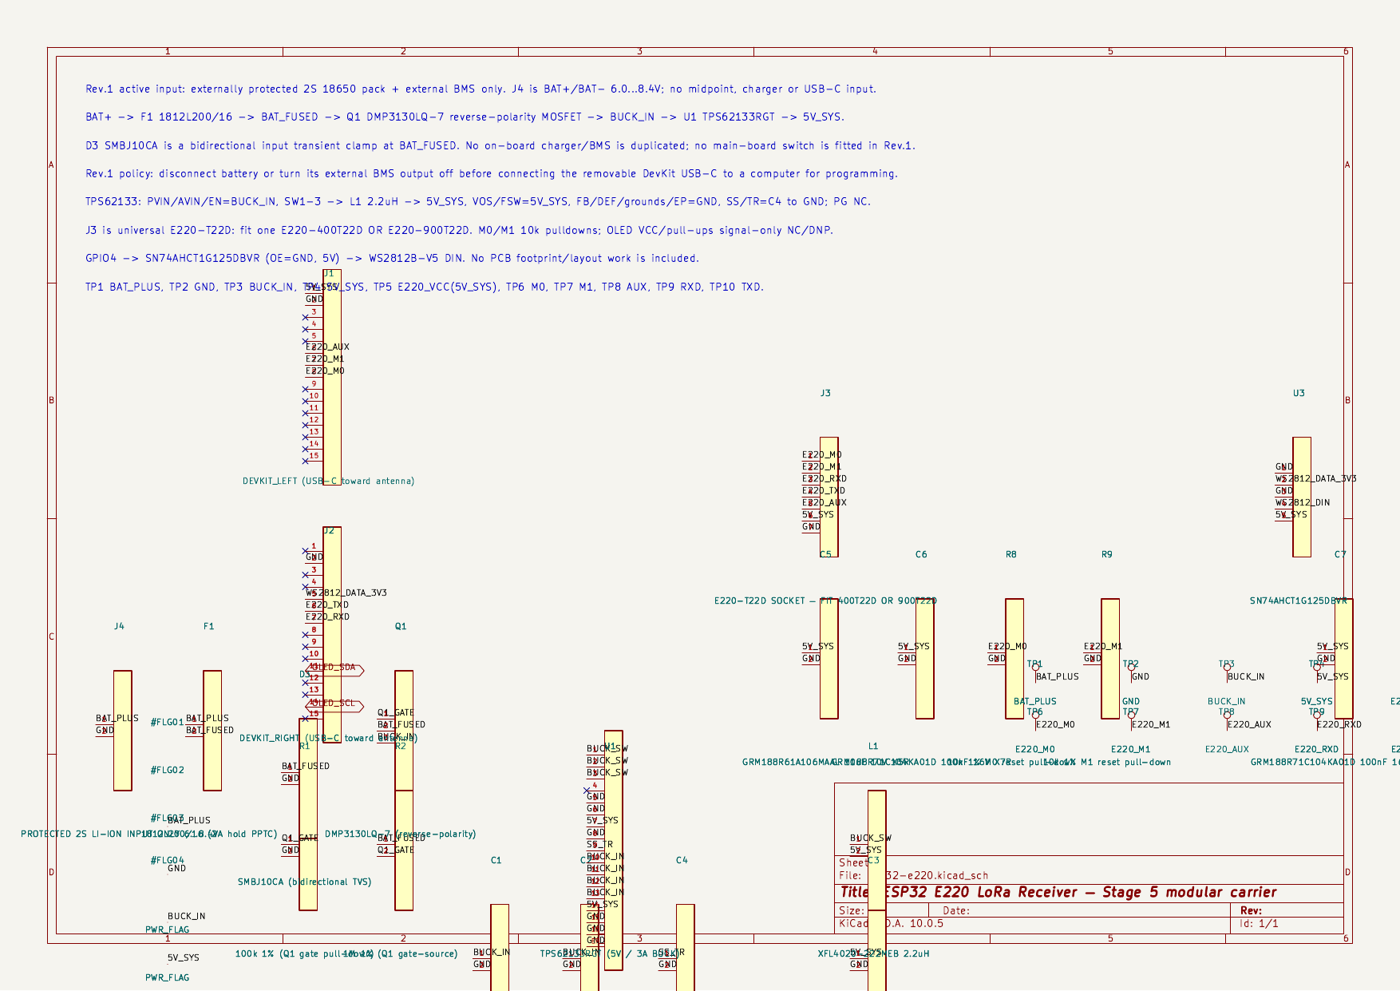
hardware/evidence/preexisting-esp32-e220-artifacts/esp32-e220-rev1.png
