kvderevyanko/klicad/hardware/evidence/preexisting-esp32-e220-artifacts/esp32-e220-schematic-preview.png

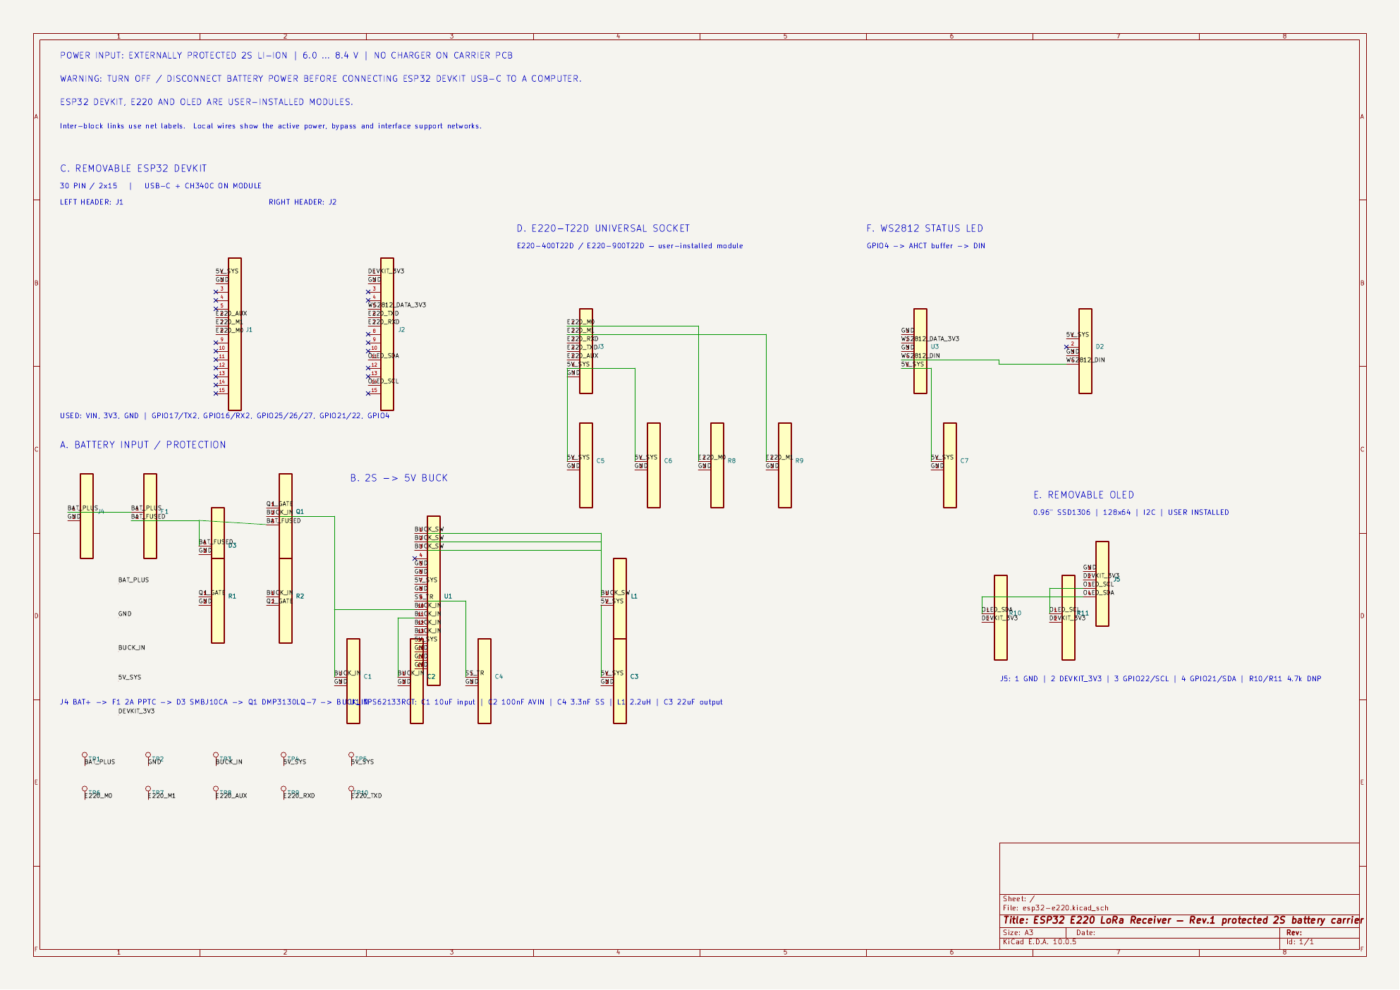
hardware/evidence/preexisting-esp32-e220-artifacts/esp32-e220-schematic-preview.png
