kvderevyanko/klicad/hardware/evidence/preexisting-esp32-e220-artifacts/layout-smoke.png

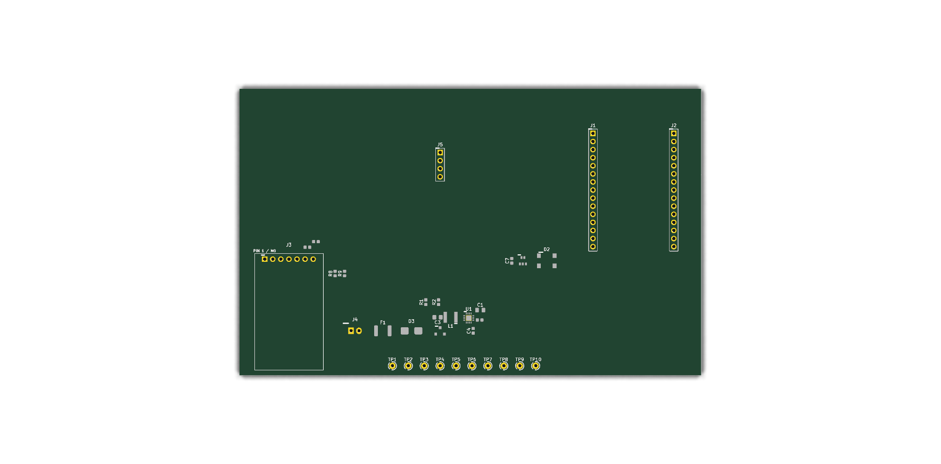
hardware/evidence/preexisting-esp32-e220-artifacts/layout-smoke.png
