kvderevyanko/klicad/hardware/evidence/preexisting-esp32-e220-artifacts/reviewer-placement.png

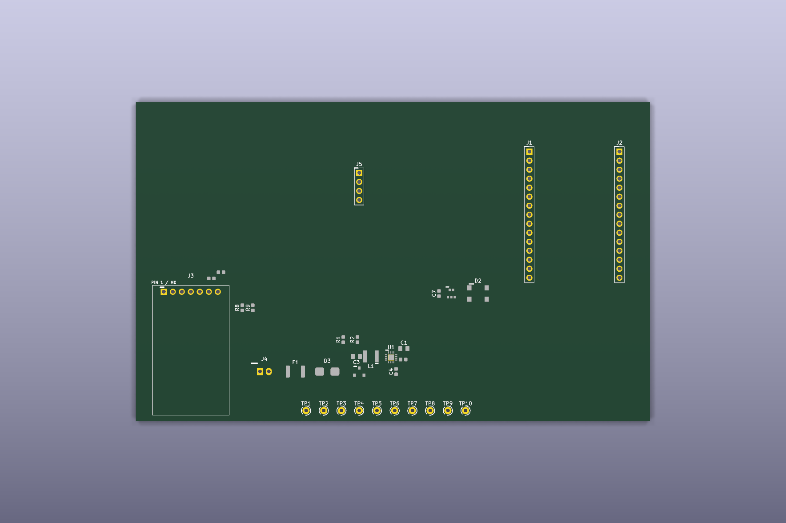
hardware/evidence/preexisting-esp32-e220-artifacts/reviewer-placement.png
