kvderevyanko/klicad/hardware/evidence/preexisting-esp32-e220-artifacts/samtec-ssw-s-review-1.png

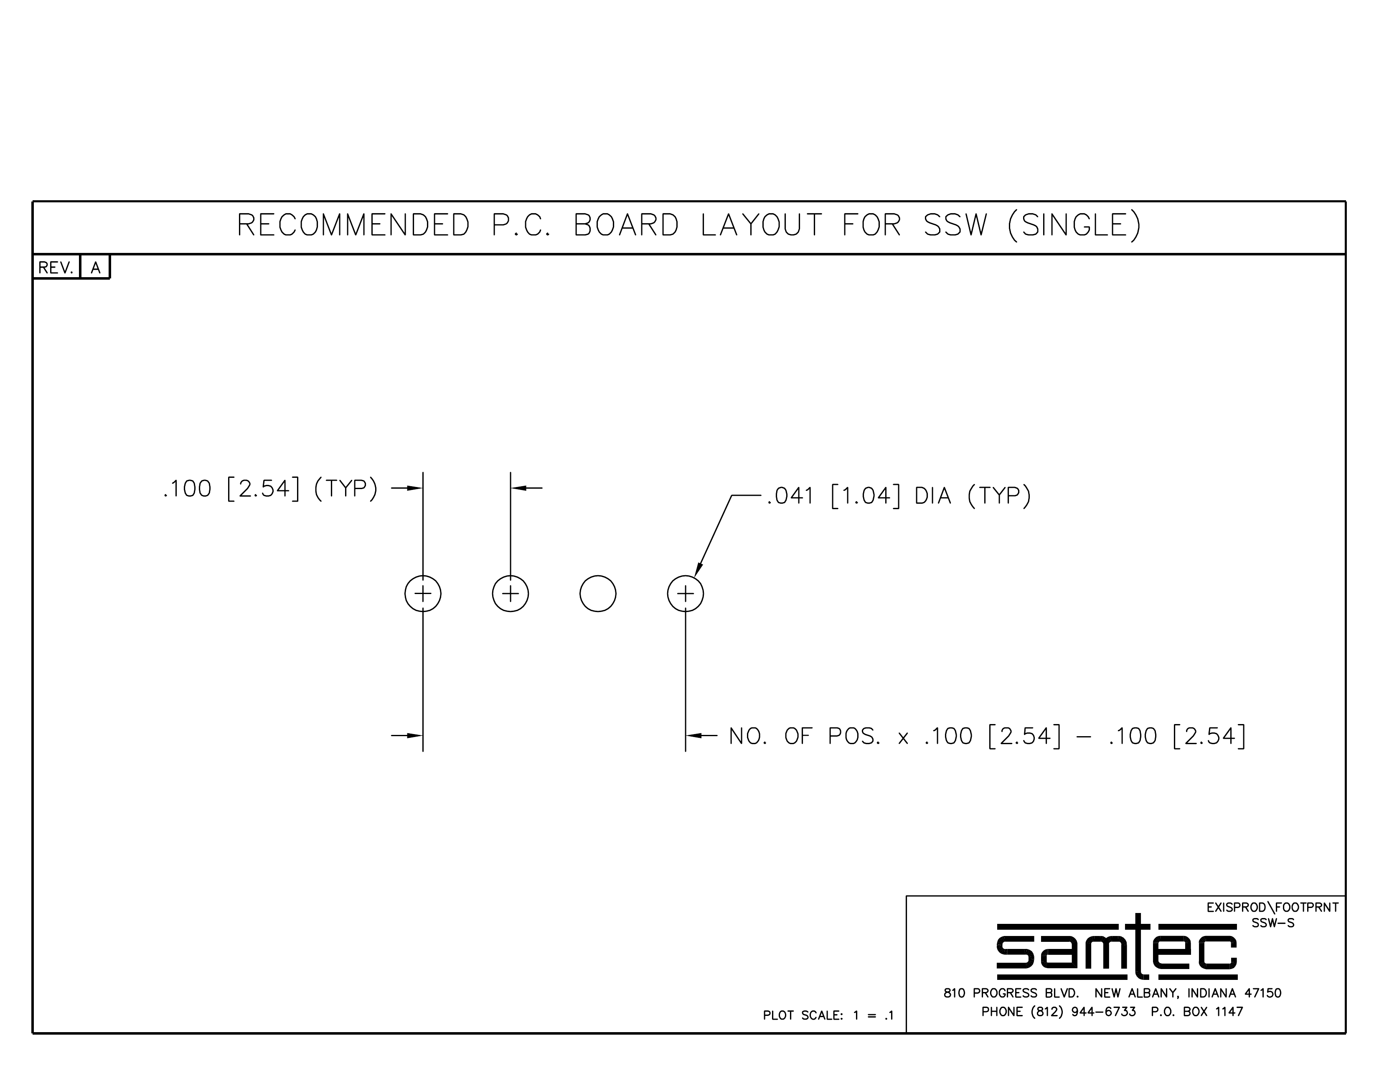
hardware/evidence/preexisting-esp32-e220-artifacts/samtec-ssw-s-review-1.png
