kvderevyanko/klicad/hardware/evidence/preexisting-esp32-e220-artifacts/stage8-placement.png

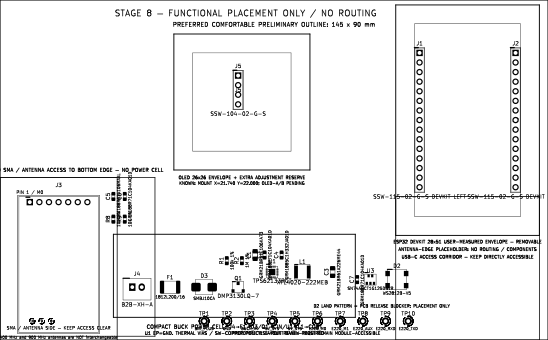
hardware/evidence/preexisting-esp32-e220-artifacts/stage8-placement.png
