kvderevyanko/klicad/hardware/evidence/preexisting-esp32-e220-artifacts/tps62133-page-30.png

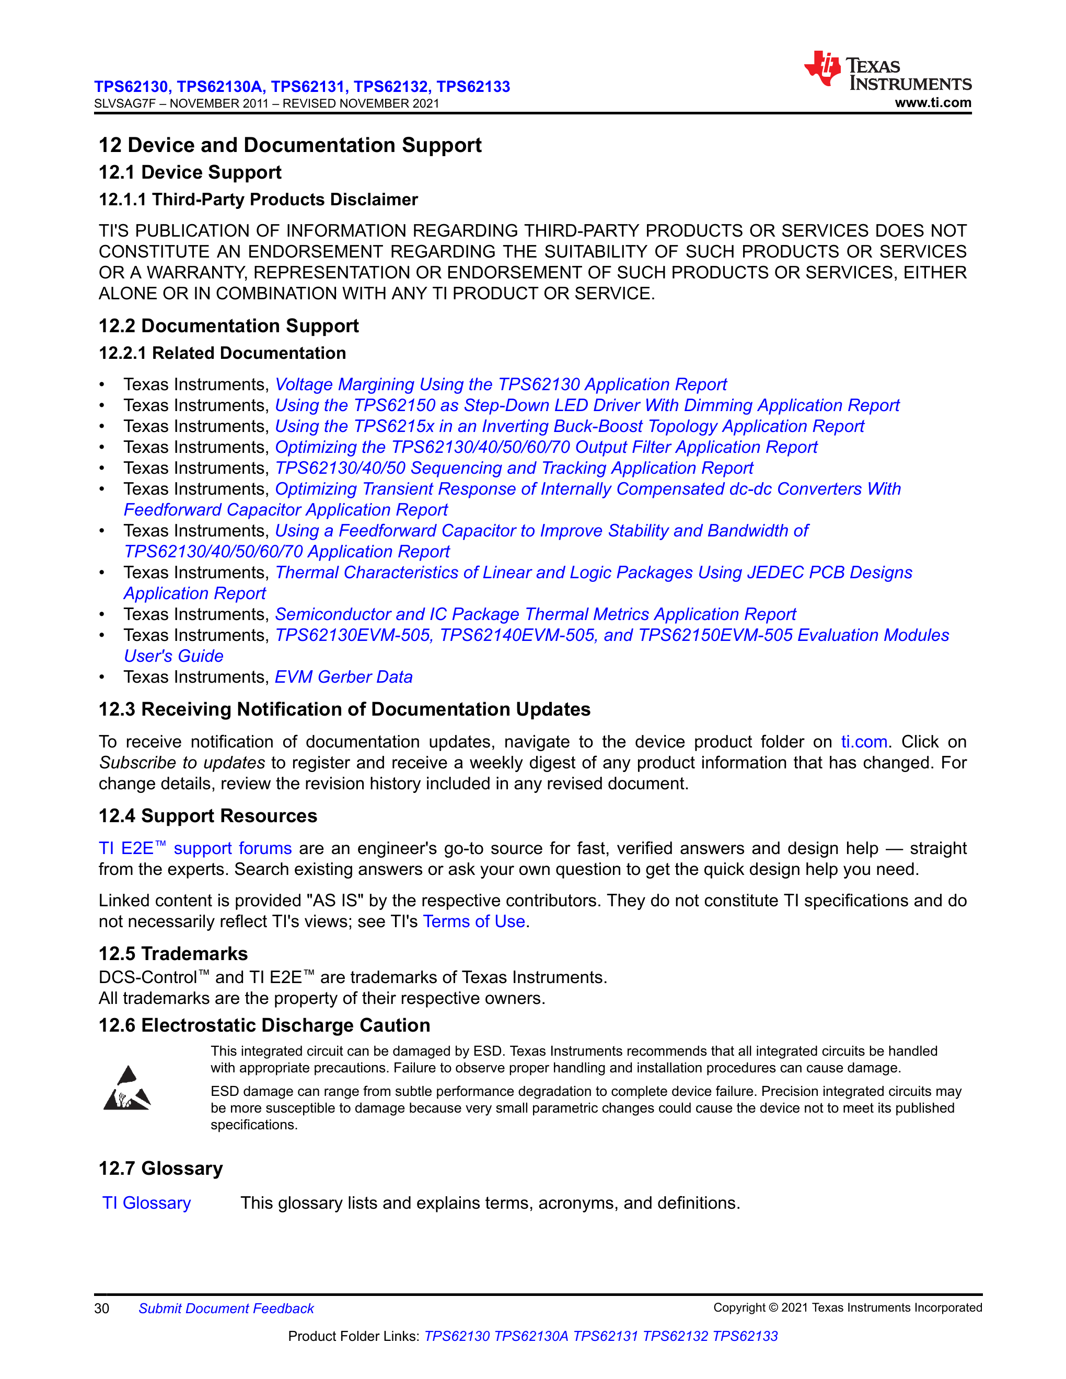
hardware/evidence/preexisting-esp32-e220-artifacts/tps62133-page-30.png
