kvderevyanko/klicad/hardware/evidence/q1-production-error-2026-09-11/Diodes-DMP3130LQ-DS38728-page5.png

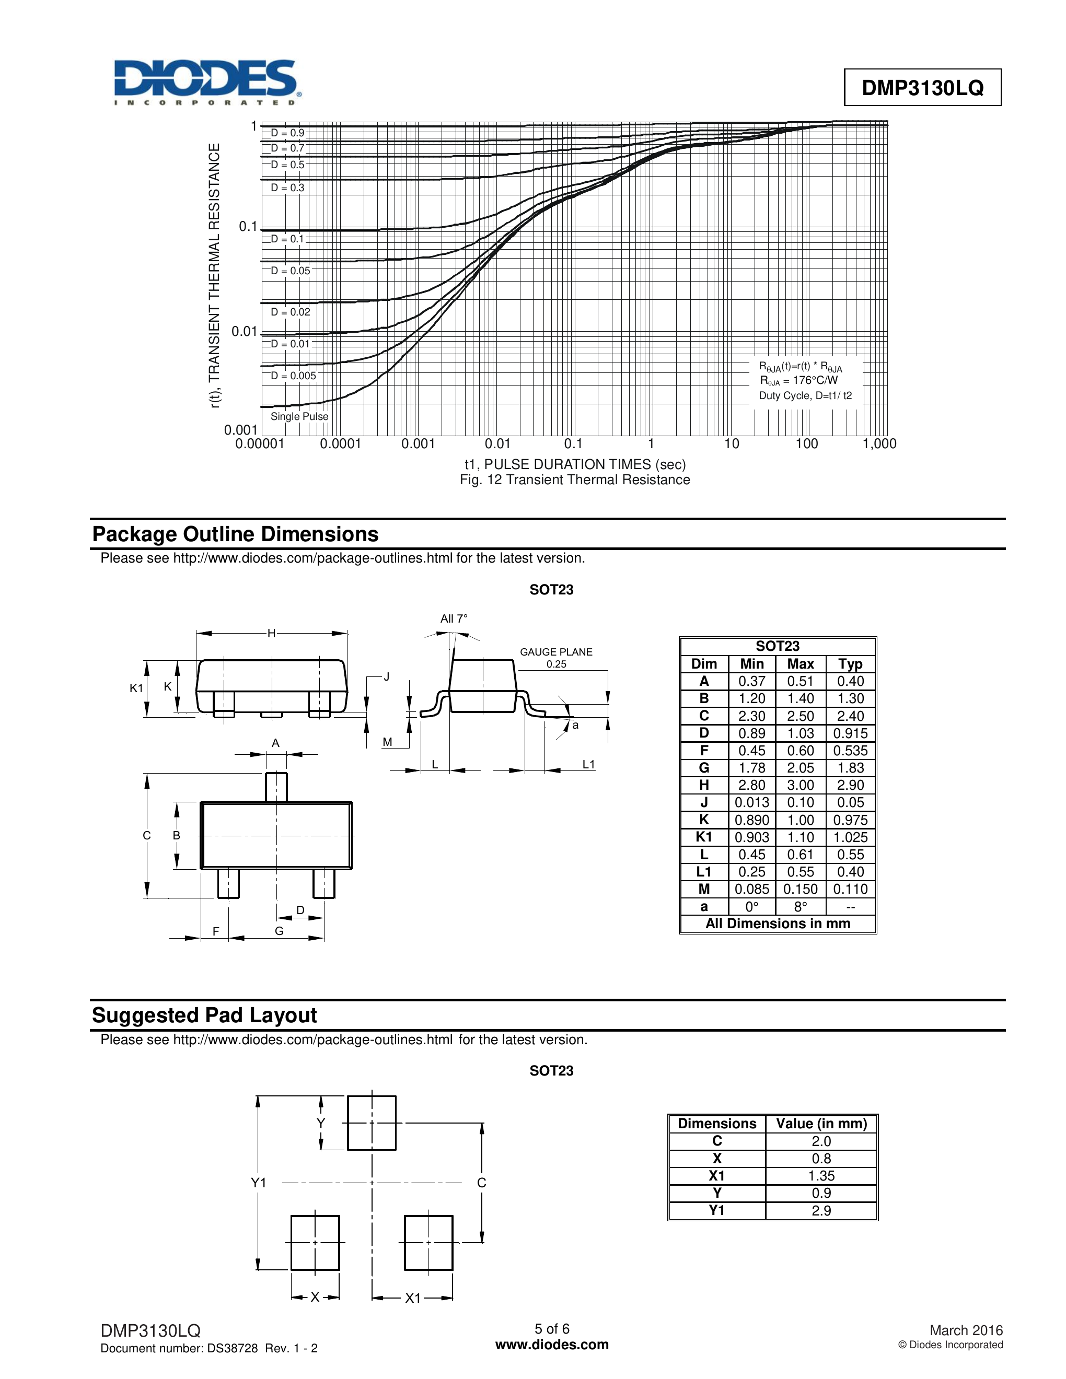
hardware/evidence/q1-production-error-2026-09-11/Diodes-DMP3130LQ-DS38728-page5.png
