kvderevyanko/klicad/hardware/evidence/q1-production-error-2026-09-11/Diodes-SOT23-package-page1-400dpi.png

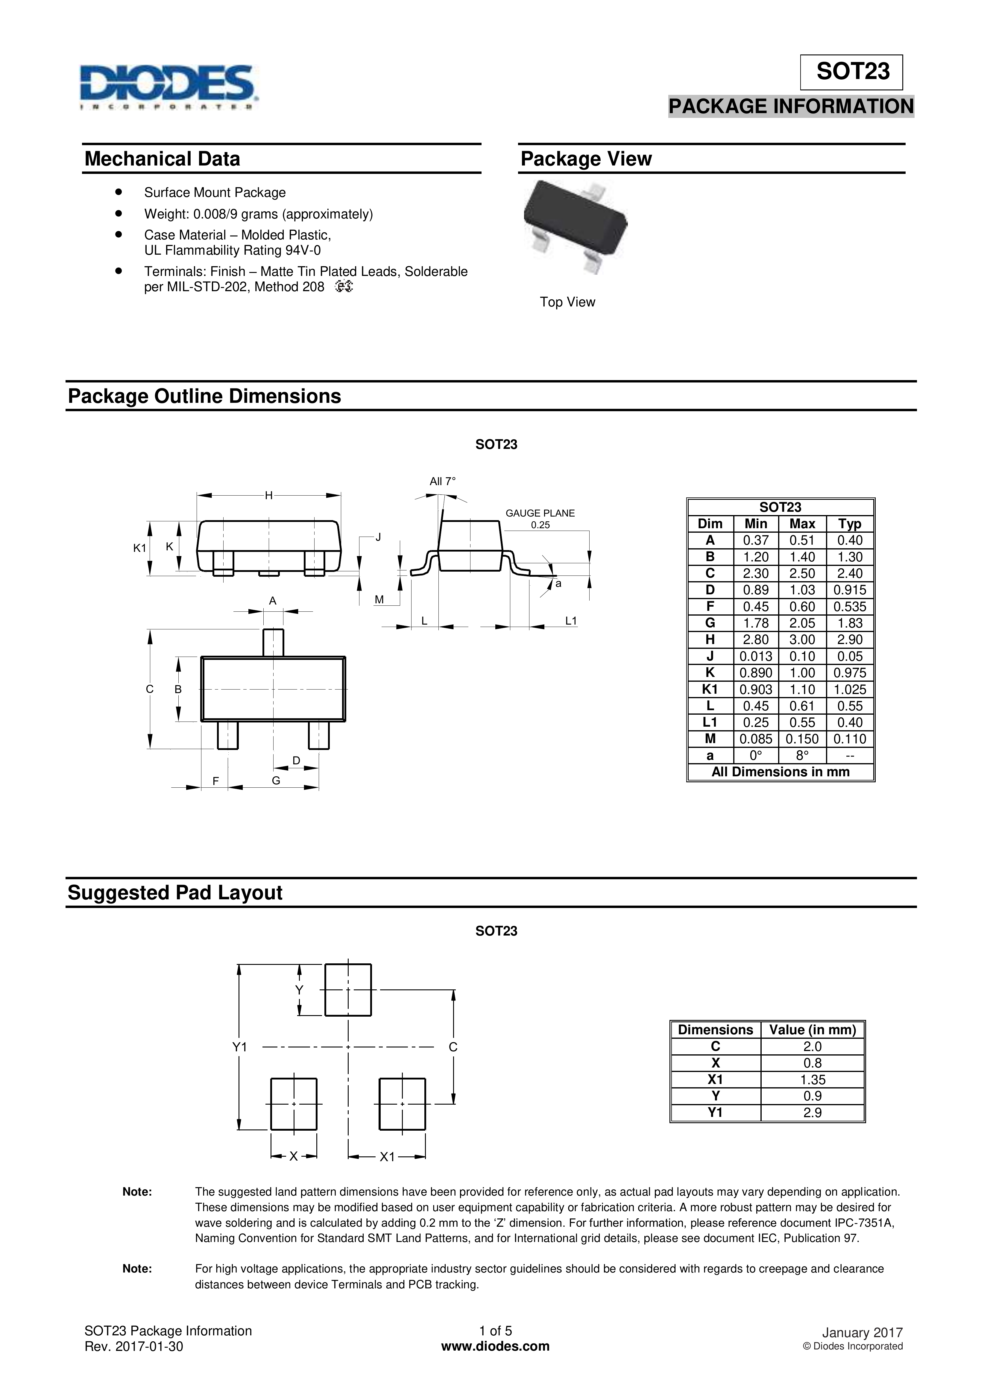
hardware/evidence/q1-production-error-2026-09-11/Diodes-SOT23-package-page1-400dpi.png
