kvderevyanko/klicad/hardware/evidence/rev1-connectivity-completion-2026-08-21/00-active-copper.png

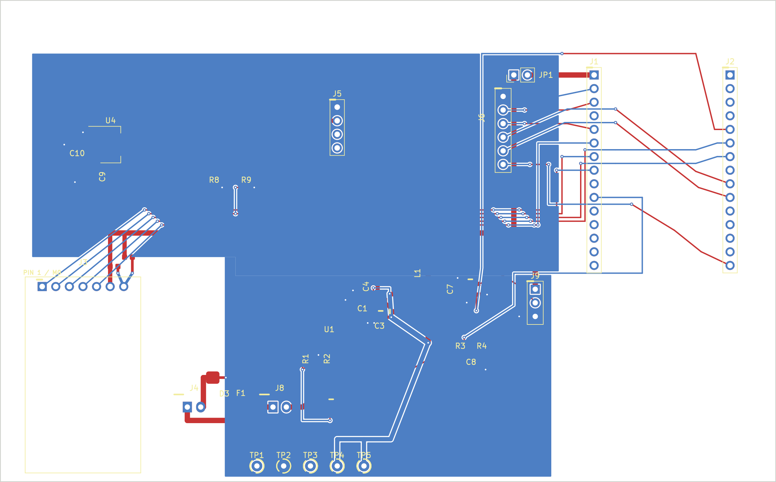
hardware/evidence/rev1-connectivity-completion-2026-08-21/00-active-copper.png
