kvderevyanko/klicad/hardware/evidence/rev1-j5-m3-plan-2026-08-21/20-candidate-B_Cu.png

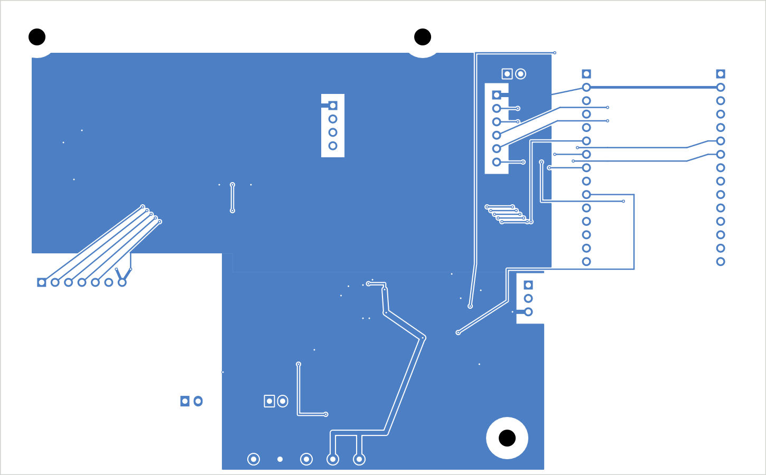
hardware/evidence/rev1-j5-m3-plan-2026-08-21/20-candidate-B_Cu.png
