kvderevyanko/klicad/hardware/evidence/rev1-j5-m3-plan-2026-08-21/21-candidate-F_Cu.png

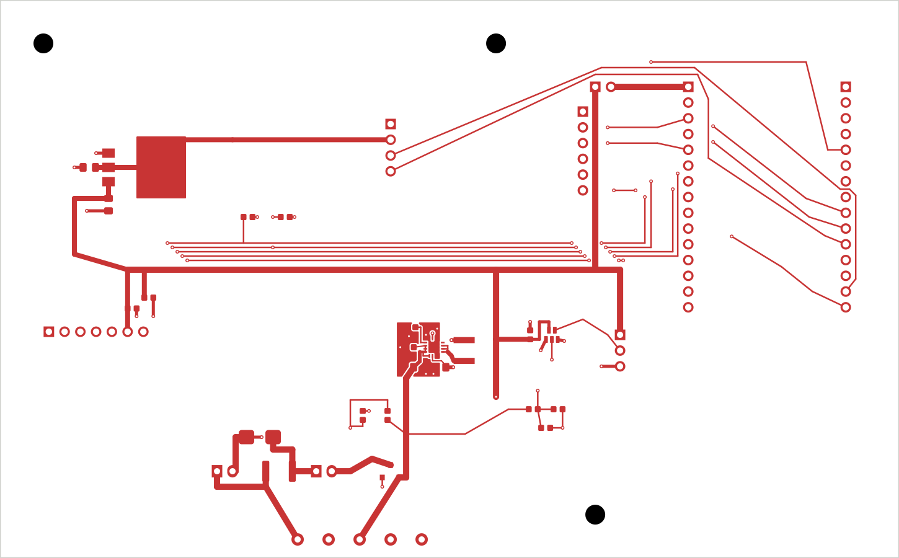
hardware/evidence/rev1-j5-m3-plan-2026-08-21/21-candidate-F_Cu.png
