kvderevyanko/klicad/hardware/evidence/rev1-j5-m3-plan-2026-08-21/22-J5-B_Cu-closeup.png

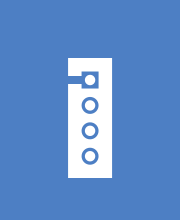
hardware/evidence/rev1-j5-m3-plan-2026-08-21/22-J5-B_Cu-closeup.png
