kvderevyanko/klicad/hardware/evidence/rev1-j5-m3-plan-2026-08-21/24-H2-B_Cu-closeup.png

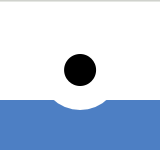
hardware/evidence/rev1-j5-m3-plan-2026-08-21/24-H2-B_Cu-closeup.png
