kvderevyanko/klicad/hardware/evidence/rev1-j5-m3-plan-2026-08-21/25-H3-B_Cu-antenna-closeup.png

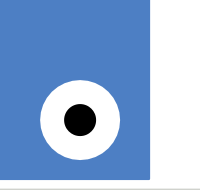
hardware/evidence/rev1-j5-m3-plan-2026-08-21/25-H3-B_Cu-antenna-closeup.png
