kvderevyanko/klicad/hardware/evidence/rev1-preproduction-silkscreen-plan-2026-08-21/00-active-top.png

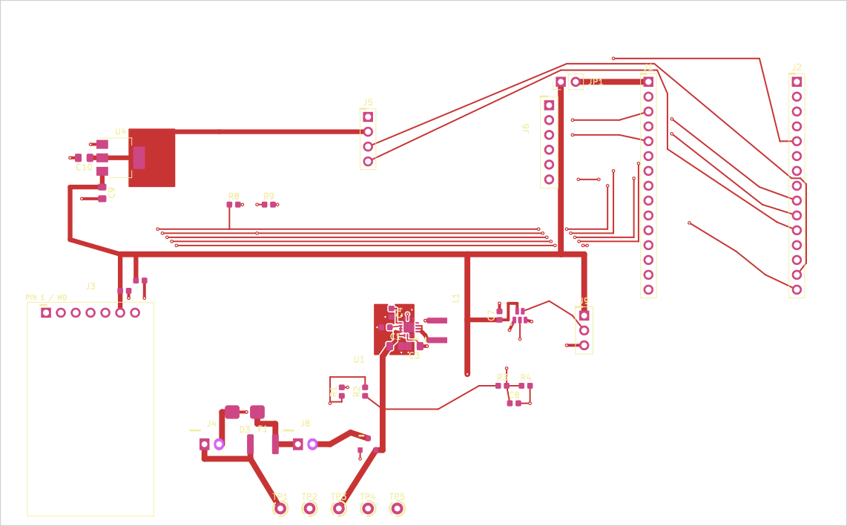
hardware/evidence/rev1-preproduction-silkscreen-plan-2026-08-21/00-active-top.png
