kvderevyanko/klicad/hardware/evidence/rev1-u4-thermal-correction-2026-08-21/ti-package-page-21.png

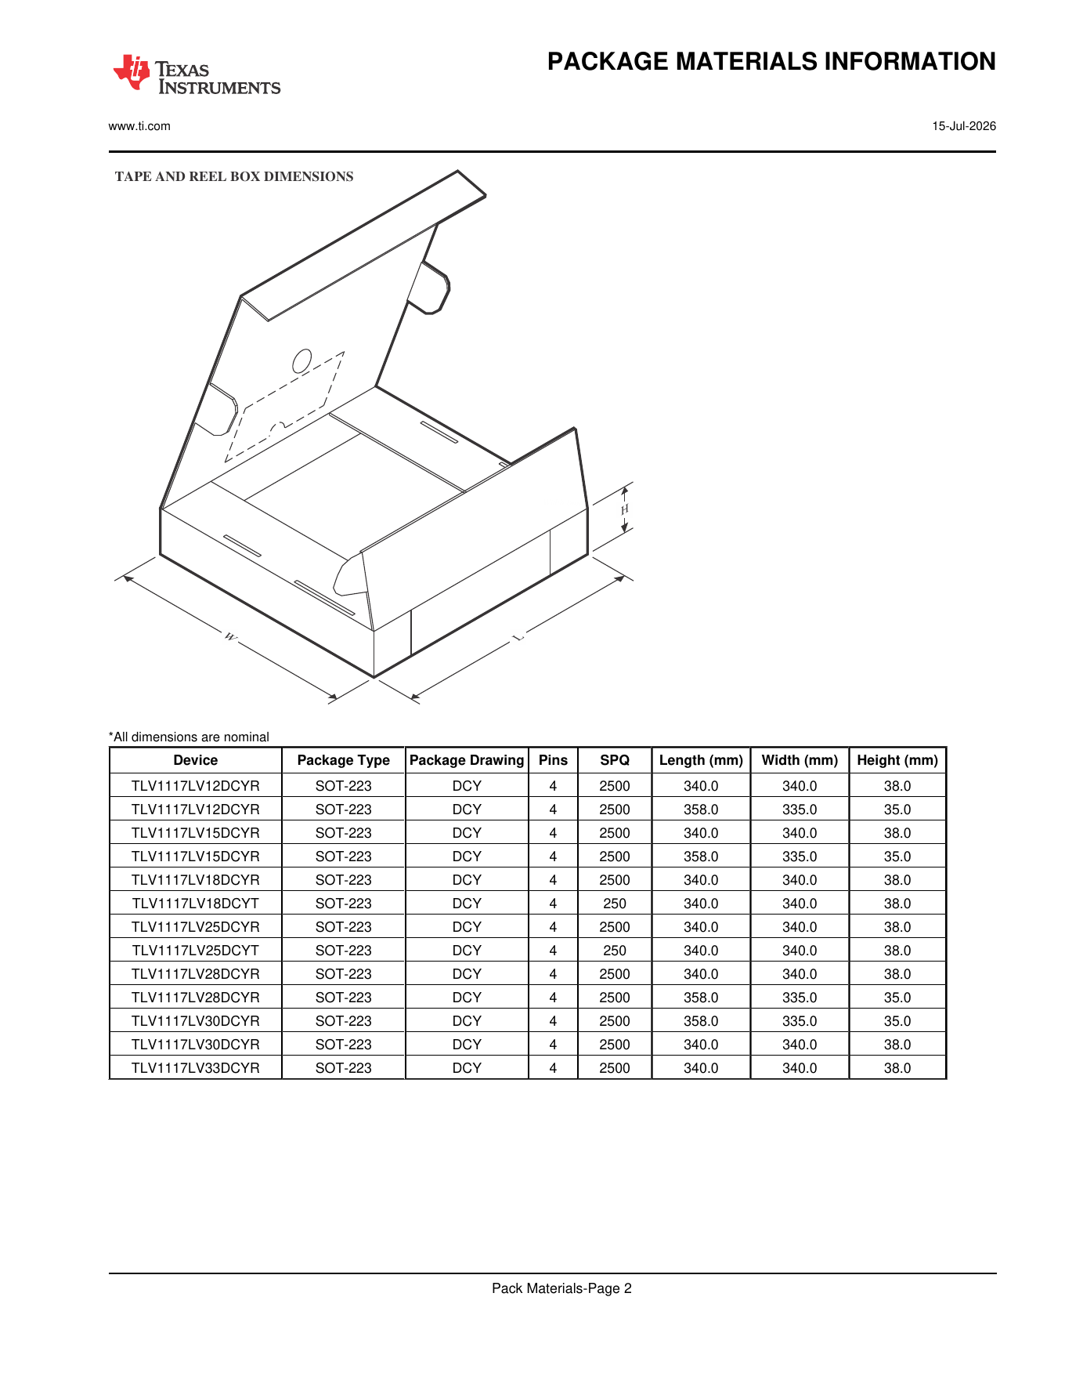
hardware/evidence/rev1-u4-thermal-correction-2026-08-21/ti-package-page-21.png
