kvderevyanko/klicad/hardware/evidence/rev1-j6-j9-handsolder-plan-2026-08-21/32-J9-B_Cu-closeup.png

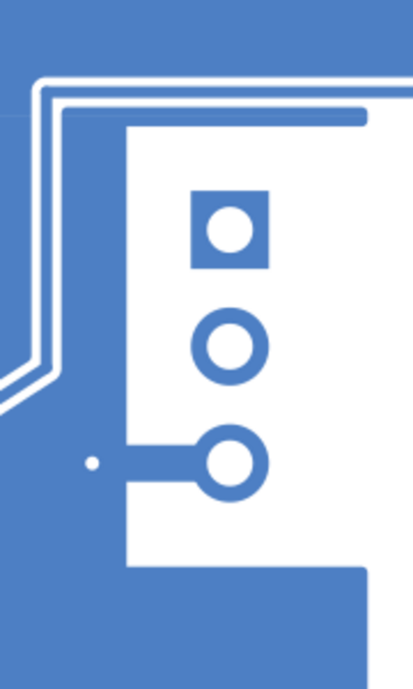
hardware/evidence/rev1-j6-j9-handsolder-plan-2026-08-21/32-J9-B_Cu-closeup.png
