kvderevyanko/klicad/hardware/evidence/rev1-preproduction-audit-2026-08-21/diagnostic-fab-courtyard.pdf

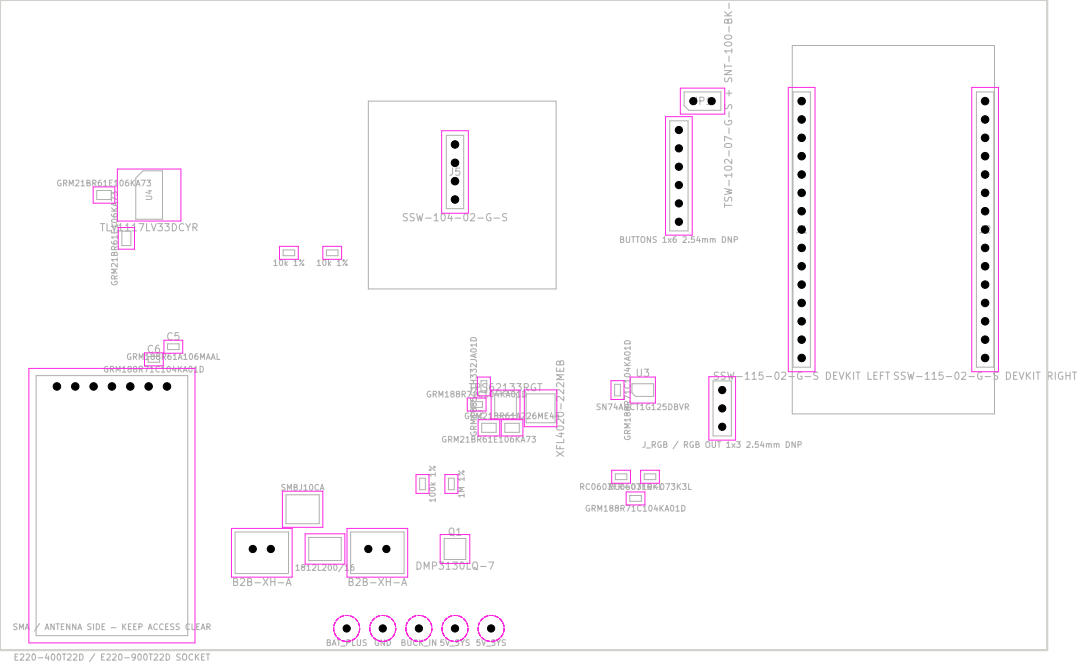
[picture p54: page 1]

J_RGB / RGB OUT 1x3 2.54mm DNP TSW-102-07-G-S + SNT-100-BK-G
