kvderevyanko/klicad/hardware/evidence/rev1-expansion-2026-08-20/esp32-e220-aux-3v3.pdf

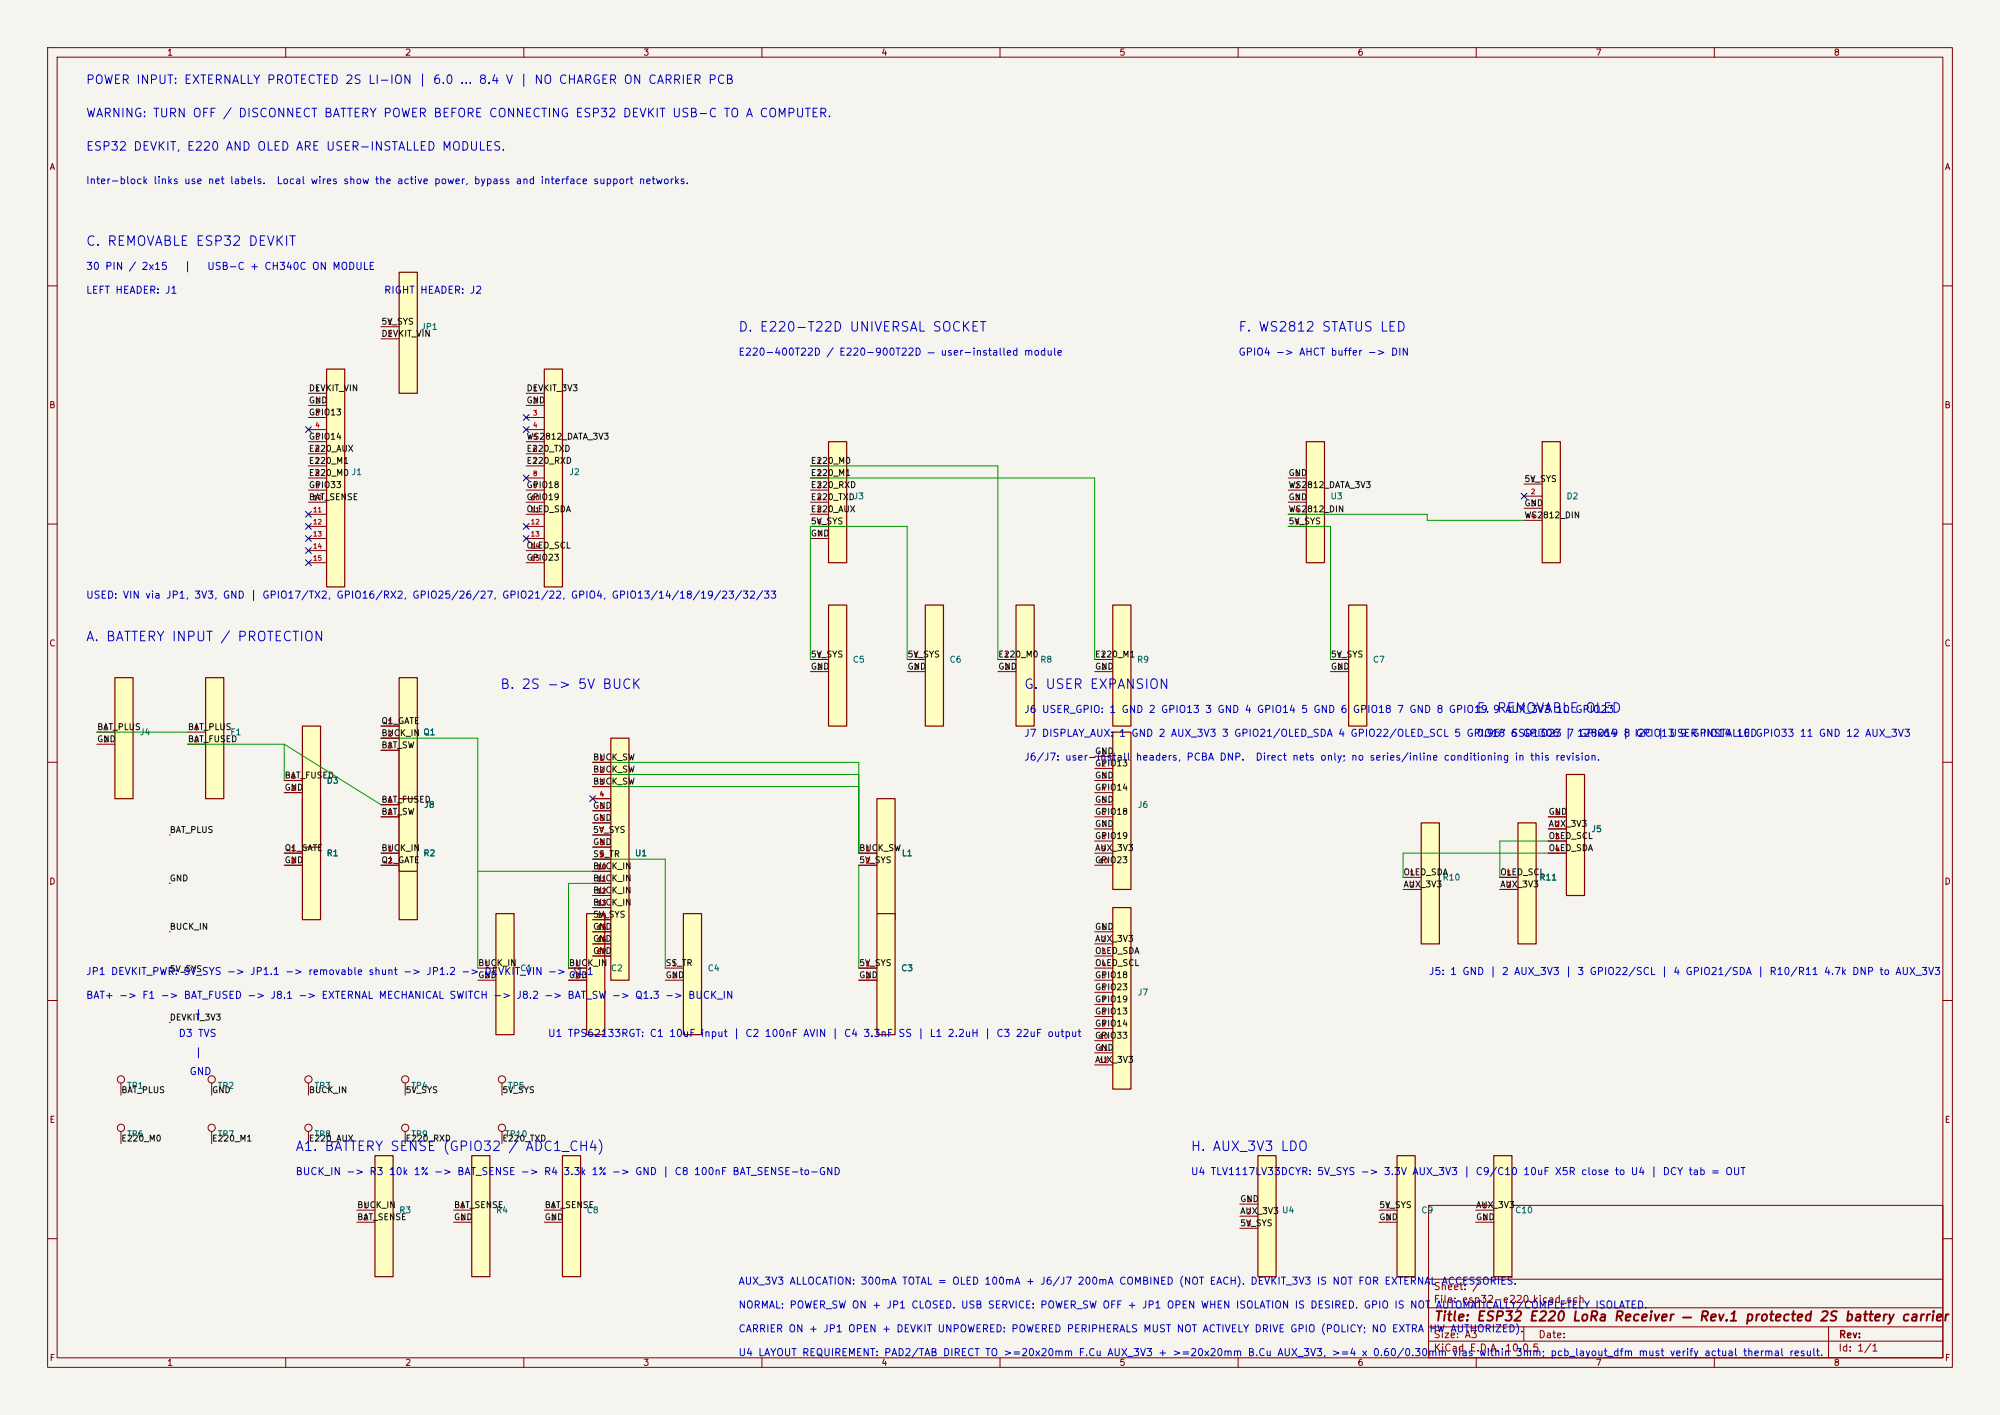
[picture p55: page 1]
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

WARNING: TURN OFF / DISCONNECT BATTERY POWER BEFORE CONNECTING ESP32 DEVKIT USB-C TO A COMPUTER.

ESP32 DEVKIT, E220 AND OLED ARE USER-INSTALLED MODULES.

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

USED: VIN via JP1, 3V3, GND | GPIO17/TX2, GPIO16/RX2, GPIO25/26/27, GPIO21/22, GPIO4, GPIO13/14/18/19/23/32/33

J5: 1 GND | 2 AUX_3V3 | 3 GPIO22/SCL | 4 GPIO21/SDA | R10/R11 4.7k DNP to AUX_3V3

U4 TLV1117LV33DCYR: 5V_SYS -> 3.3V AUX_3V3 | C9/C10 10uF X5R close to U4 | DCY tab = OUT

AUX_3V3 ALLOCATION: 300mA TOTAL = OLED 100mA + J6/J7 200mA COMBINED (NOT EACH). DEVKIT_3V3 IS NOT FOR EXTERNAL ACCESSORIES.

Sheet: /
File: esp32-e220.kicad_sch
Title: ESP32 E220 LoRa Receiver — Rev.1 protected 2S battery carrier

NORMAL: POWER_SW ON + JP1 CLOSED. USB SERVICE: POWER_SW OFF + JP1 OPEN WHEN ISOLATION IS DESIRED. GPIO IS NOT AUTOMATICALLY/COMPLETELY ISOLATED.

Size: A3 | Rev: | F Date:
KiCad E.D.A. 10.0.5 | Id: 1/1

U4 LAYOUT REQUIREMENT: PAD2/TAB DIRECT TO >=20x20mm F.Cu AUX_3V3 + >=20x20mm B.Cu AUX_3V3, >=4 x 0.60/0.30mm vias within 3mm; pcb_layout_dfm must verify actual thermal result.
