kvderevyanko/klicad/hardware/evidence/rev1-expansion-2026-08-20/esp32-e220-rev1-expansion.pdf

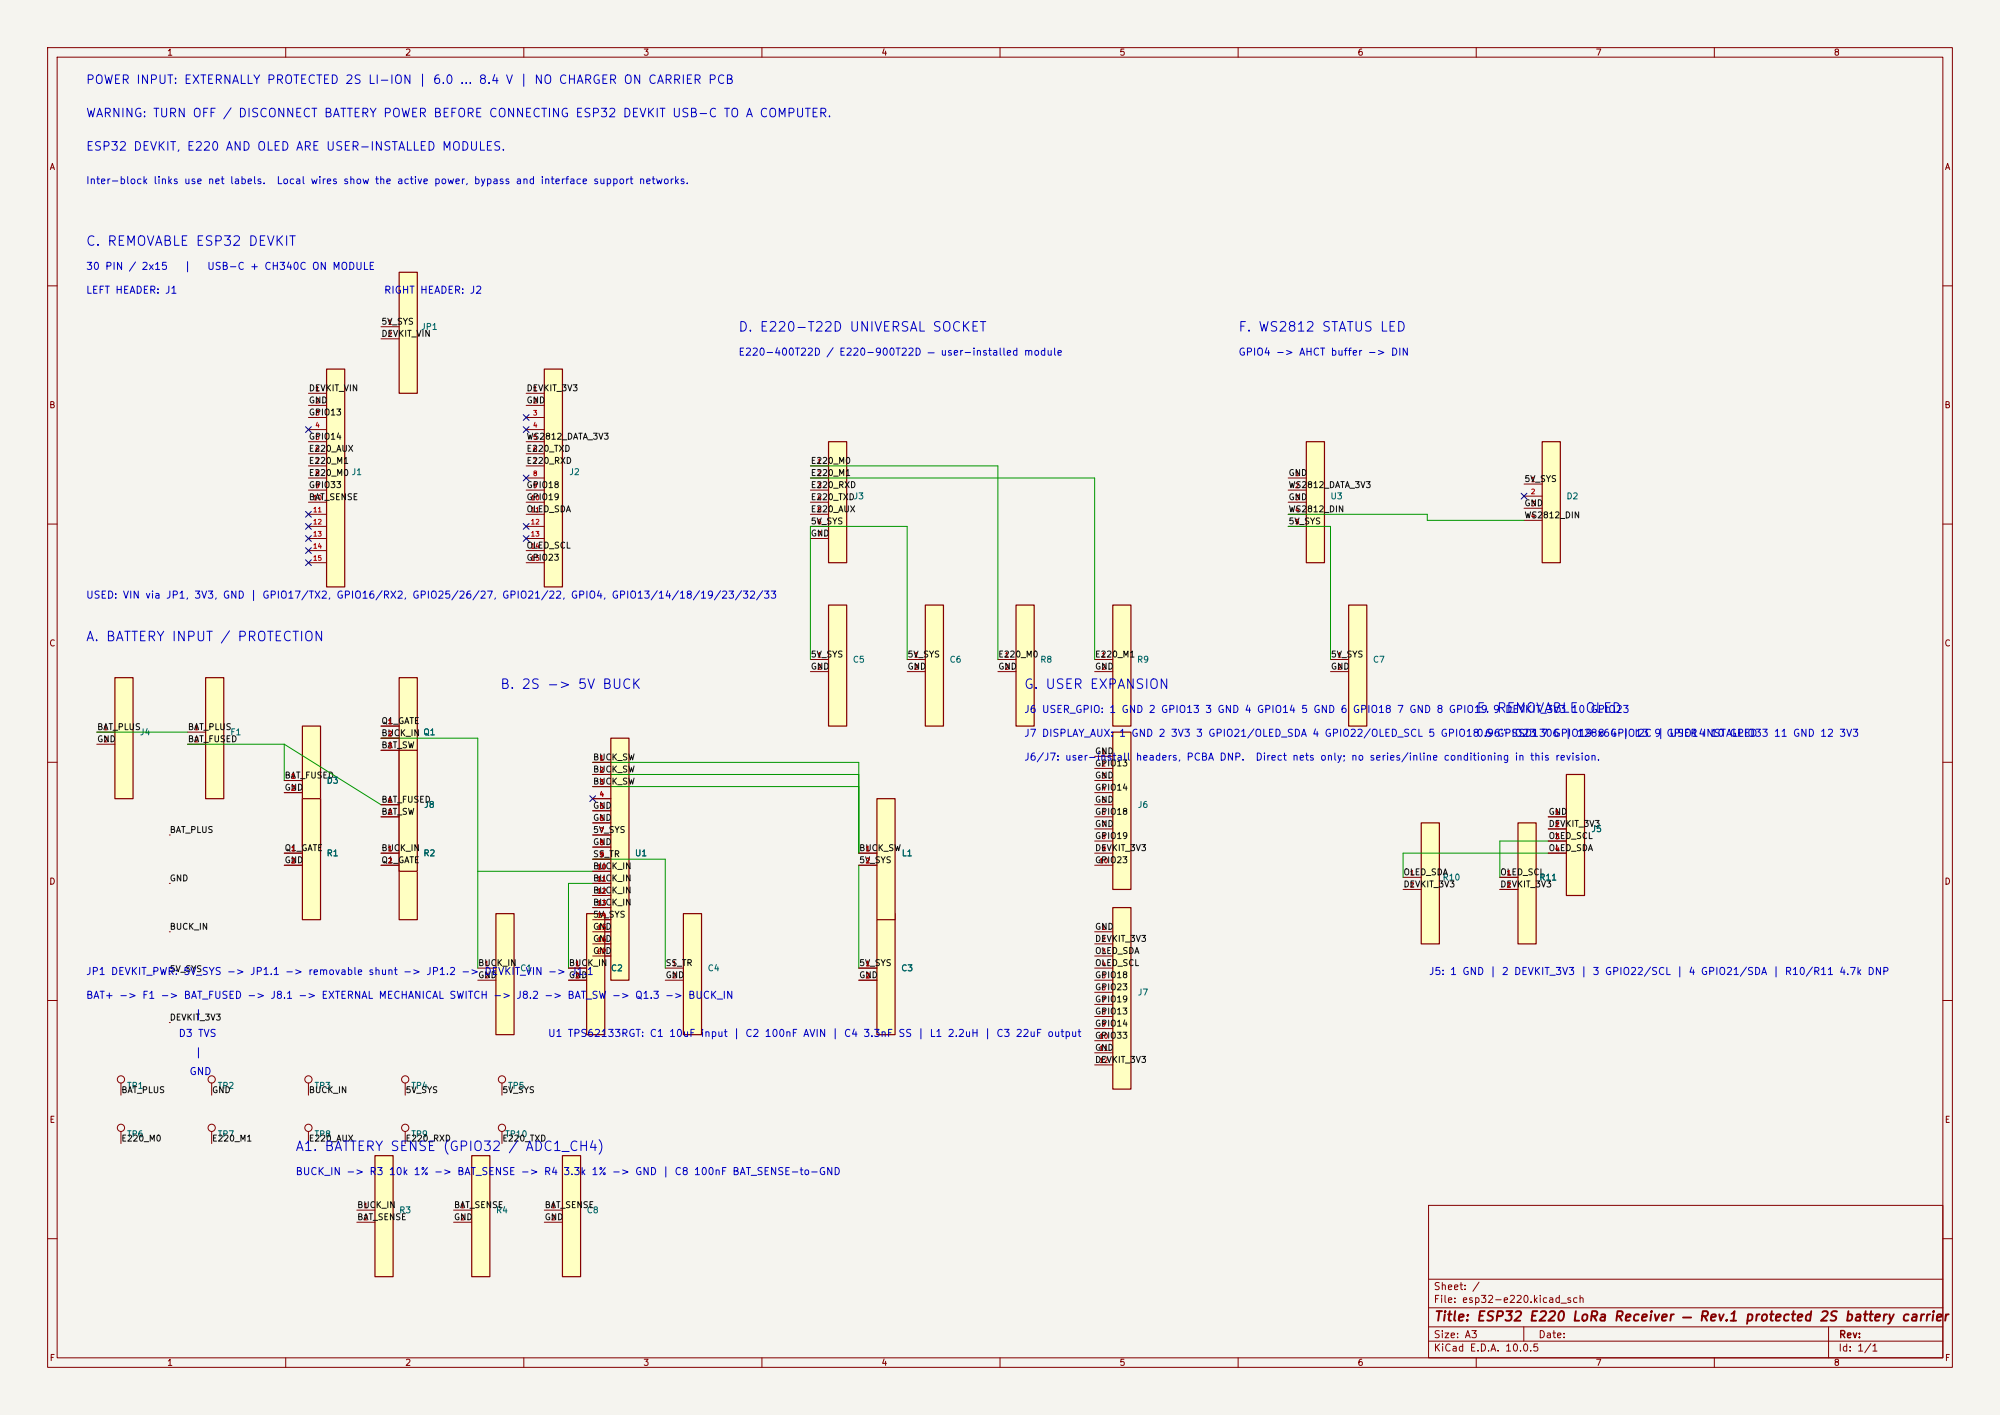
[picture p56: page 1]
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

ESP32 DEVKIT, E220 AND OLED ARE USER-INSTALLED MODULES.

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

J5: 1 GND | 2 DEVKIT_3V3 | 3 GPIO22/SCL | 4 GPIO21/SDA | R10/R11 4.7k DNP

Sheet: /
File: esp32-e220.kicad_sch
Title: ESP32 E220 LoRa Receiver — Rev.1 protected 2S battery carrier

Size: A3 | Rev: | F Date:
KiCad E.D.A. 10.0.5 | Id: 1/1
