kvderevyanko/klicad/hardware/evidence/preexisting-esp32-e220-artifacts/esp32-e220-gate2.pdf

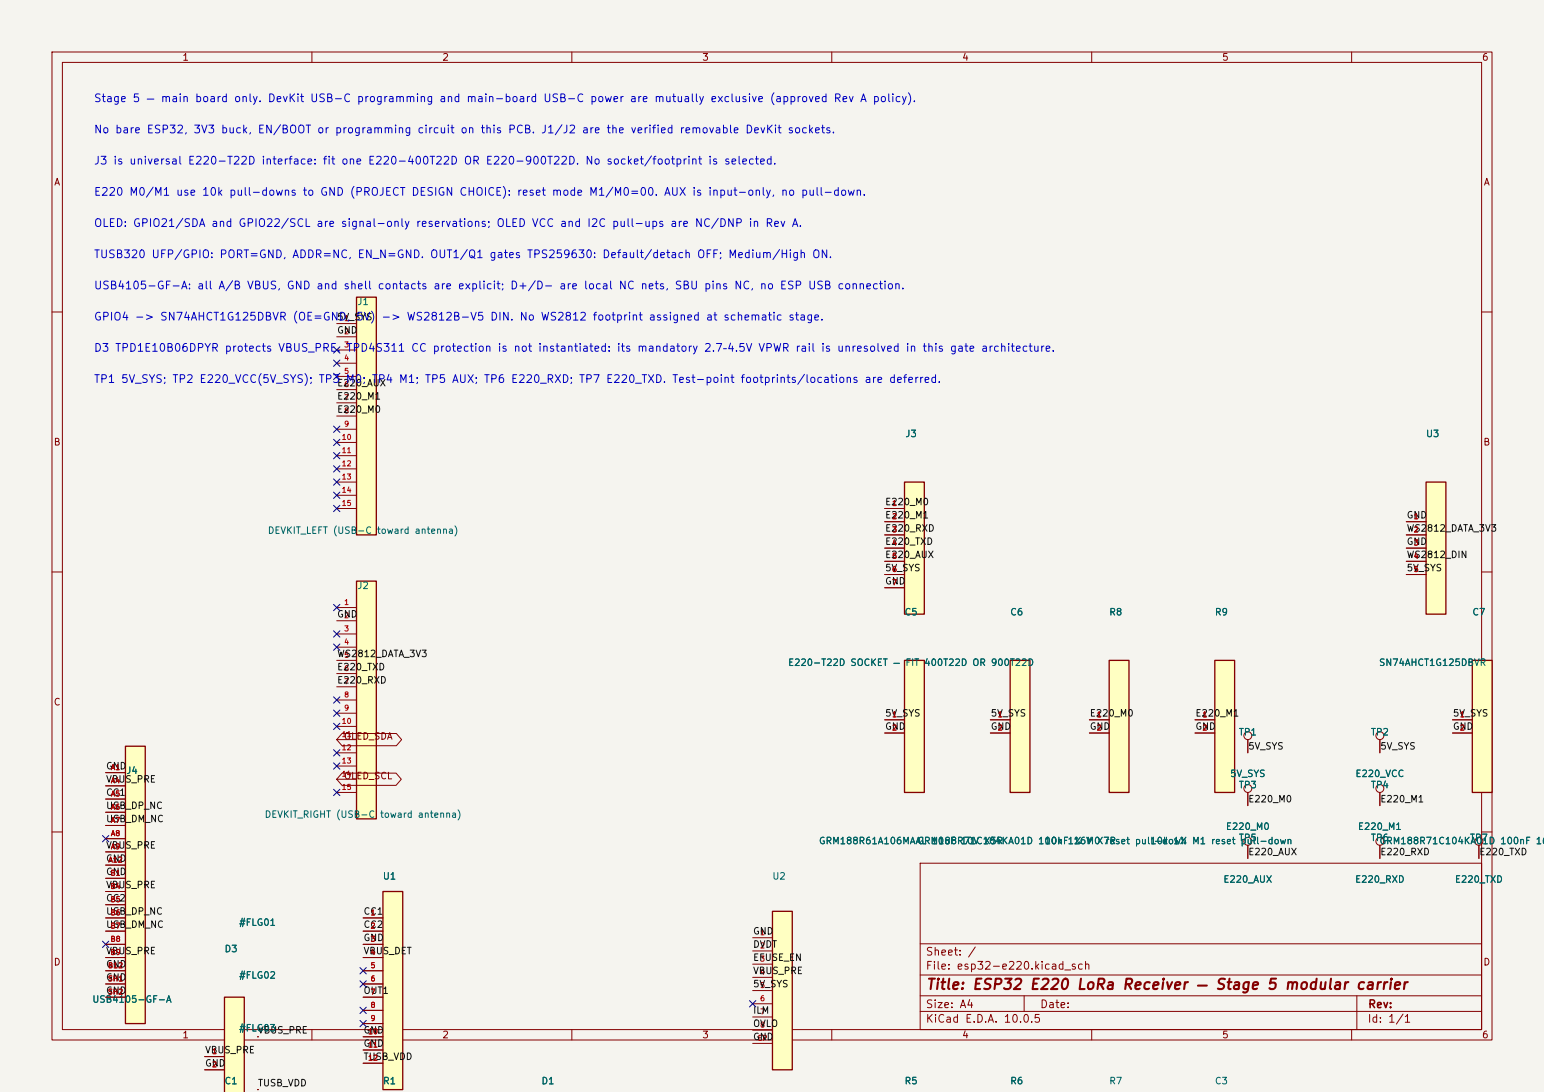
[picture p57: page 1]
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

D3 TPD1E10B06DPYR protects VBUS_PRE. TPD4S311 CC protection is not instantiated: its mandatory 2.7–4.5V VPWR rail is unresolved in this gate architecture.

TP1 5V_SYS; TP2 E220_VCC(5V_SYS); TP3 M0; TP4 M1; TP5 AUX; TP6 E220_RXD; TP7 E220_TXD. Test-point footprints/locations are deferred.

Sheet: /
File: esp32-e220.kicad_sch
Title: ESP32 E220 LoRa Receiver — Stage 5 modular carrier
KiCad E.D.A. 10.0.5
