kvderevyanko/klicad/hardware/evidence/preexisting-esp32-e220-artifacts/esp32-e220-rev1-regenerated-pro-review.pdf

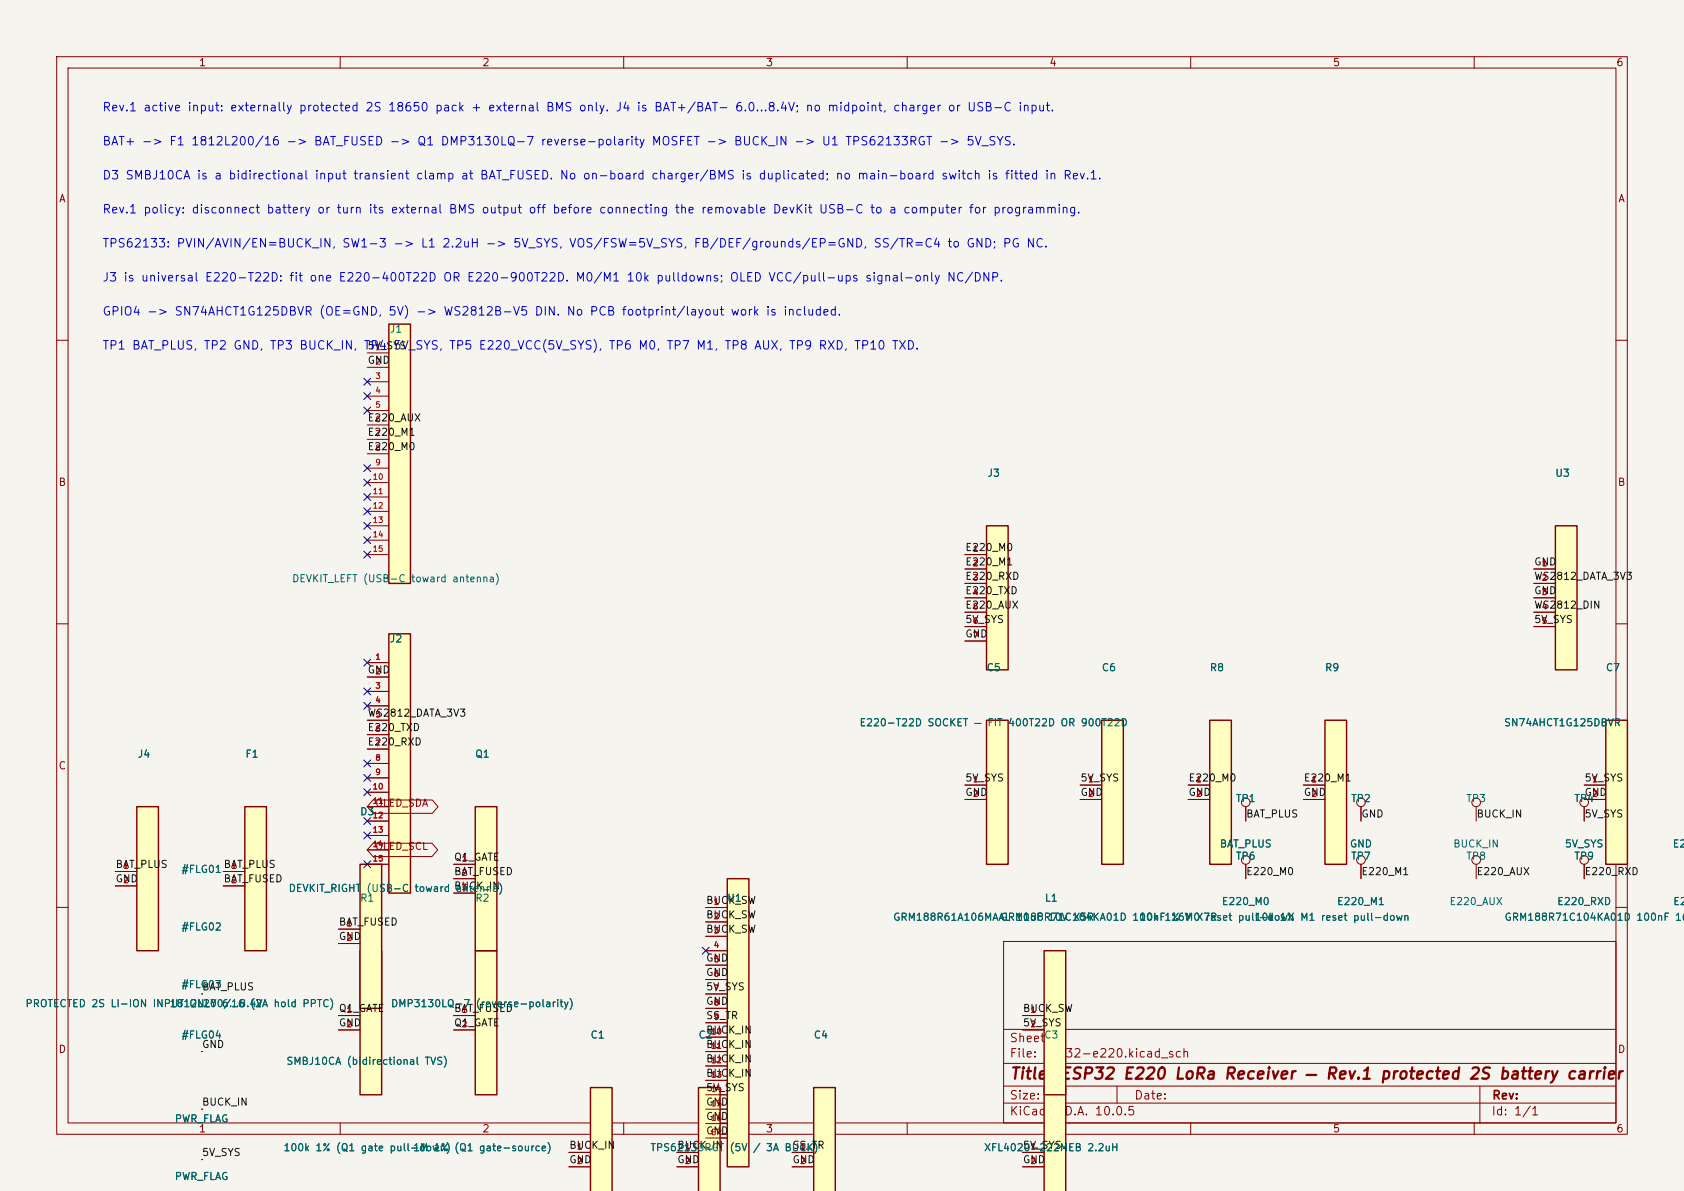
[picture p58: page 1]
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

5V_SYS D3 SMBJ10CA is a bidirectional input transient clamp at BAT_FUSED. No on-board charger/BMS is duplicated; no main-board switch is fitted in Rev.1.

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

J3 is universal E220-T22D: fit one E220-400T22D OR E220-900T22D. M0/M1 10k pulldowns; OLED VCC/pull-ups signal-only NC/DNP.

GPIO4 -> SN74AHCT1G125DBVR (OE=GND, 5V) -> WS2812B-V5 DIN. No PCB footprint/layout work is included.

2 J4 PROTECTED 2S LI-ION INPUT ONLY 6...8.4V

J4 PROTECTED 2S LI-ION INPUT ONLY 6...8.4V

Sheet: /
Title: ESP32 E220 LoRa Receiver — Rev.1 protected 2S battery carrier
KiCad E.D.A. 10.0.5
