kvderevyanko/klicad/hardware/evidence/preexisting-esp32-e220-artifacts/esp32-e220.pdf

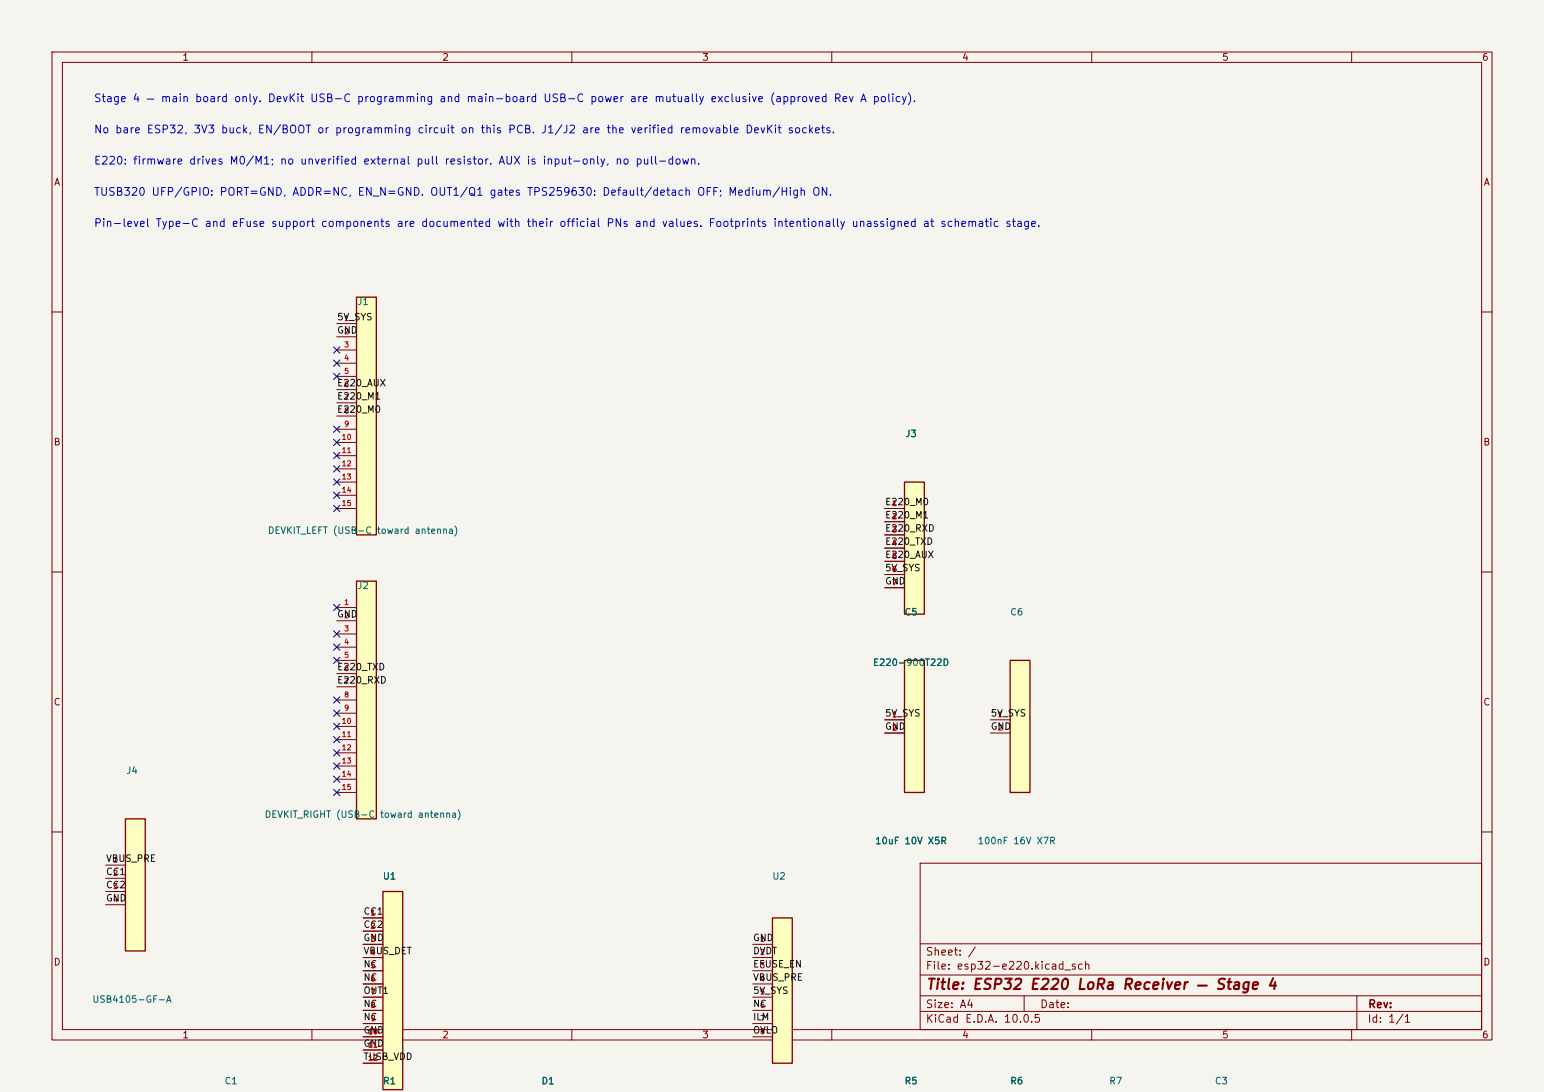
[picture p59: page 1]

Stage 4 — main board only. DevKit USB-C programming and main-board USB-C power are mutually exclusive (approved Rev A policy).

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

E220: firmware drives M0/M1; no unverified external pull resistor. AUX is input-only, no pull-down.

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

E220_AUX Pin-level Type-C and eFuse support components are documented with their official PNs and values. Footprints intentionally unassigned at schematic stage.

Sheet: /
File: esp32-e220.kicad_sch
Title: ESP32 E220 LoRa Receiver — Stage 4

Size: A4 | Rev:
KiCad E.D.A. 10.0.5 | Id: 1/1
