kvderevyanko/klicad/hardware/releases/rev1-q1-footprint-correction-2026-09-11/documentation/assembly-top.pdf

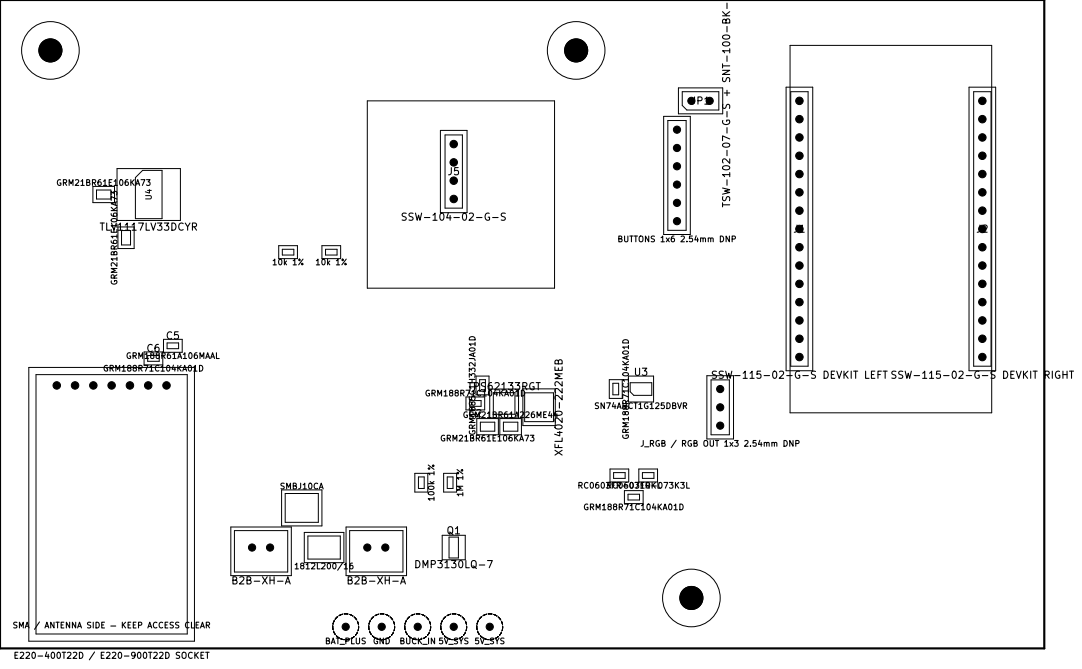
[picture p60: page 1]

J_RGB / RGB OUT 1x3 2.54mm DNP TSW-102-07-G-S + SNT-100-BK-G
