kvderevyanko/klicad/hardware/evidence/rev1-preproduction-audit-2026-08-21/diagnostic-bcu-edge.pdf

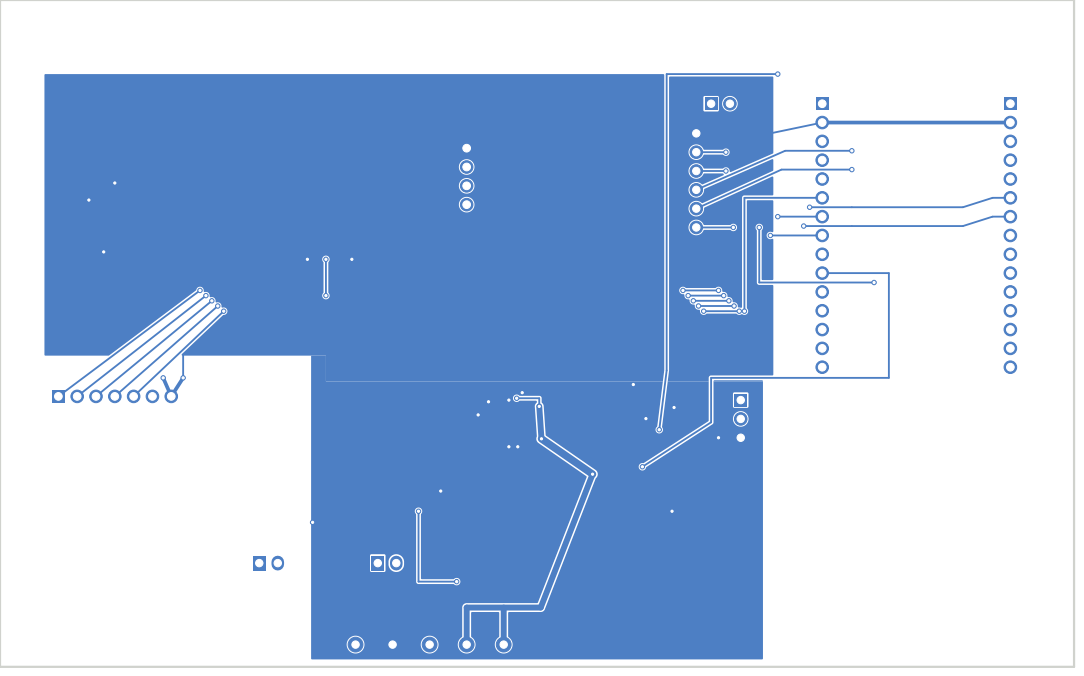
[picture p62: page 1]
