kvderevyanko/klicad/hardware/evidence/rev1-preproduction-audit-2026-08-21/diagnostic-drill-map.pdf

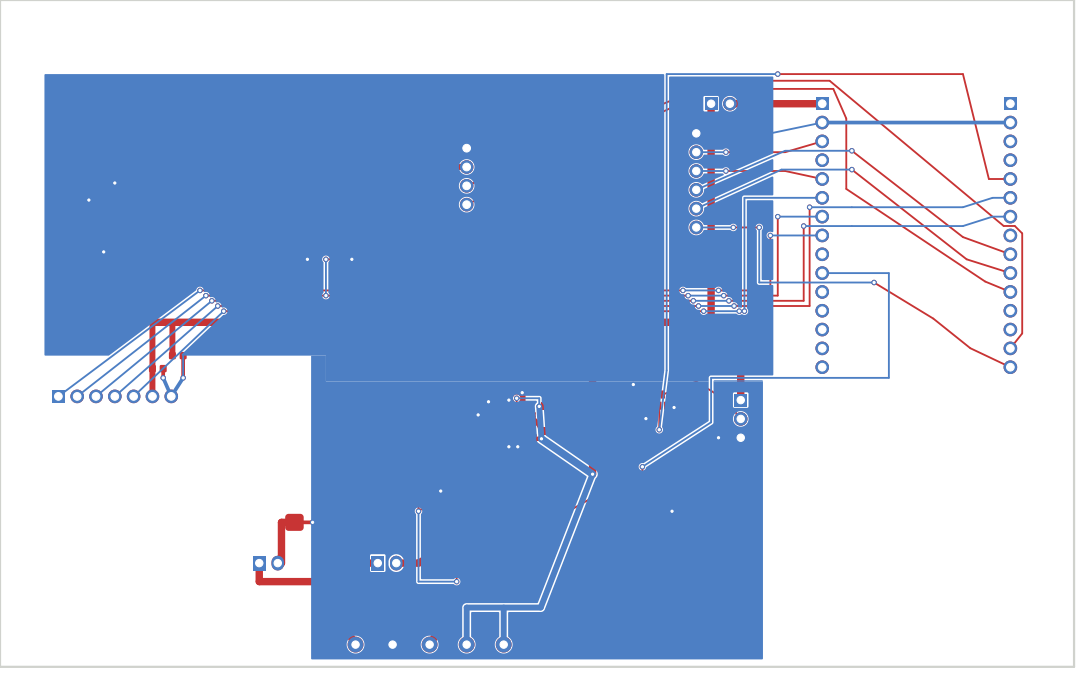
[picture p63: page 1]
