kvderevyanko/klicad/hardware/evidence/rev1-preproduction-audit-2026-08-21/diagnostic-fcu-silk-edge.pdf

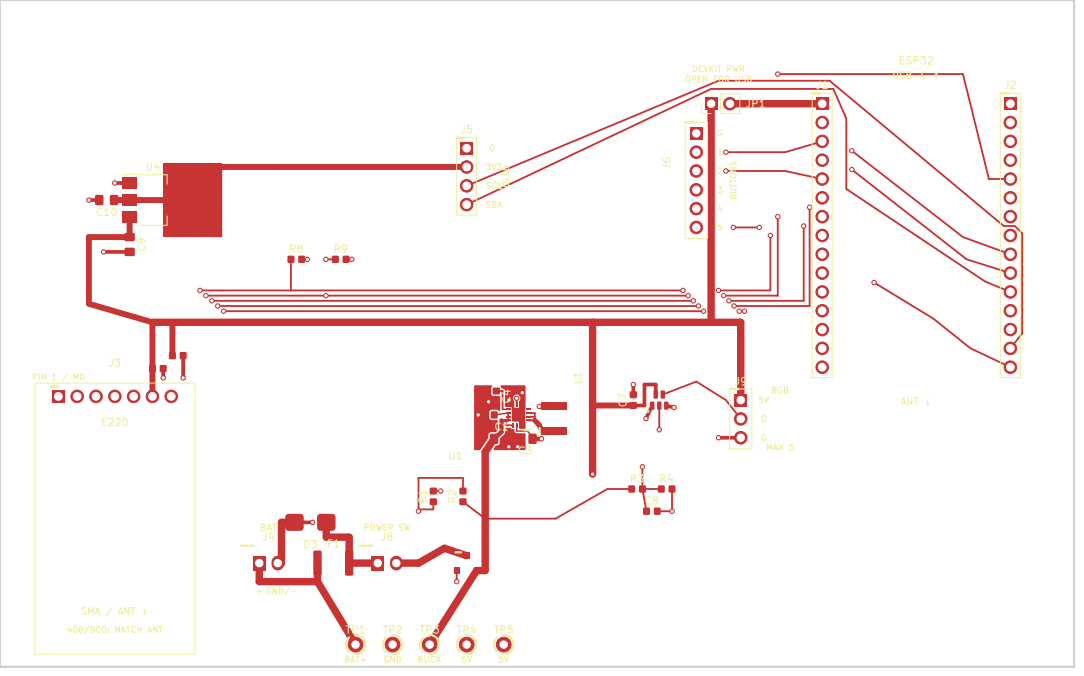
[picture p64: page 1]

DEVKIT PWR OPEN FOR USB OLED
