kvderevyanko/klicad/hardware/evidence/rev1-preproduction-audit-2026-08-21/diagnostic-fsilk-mask.pdf

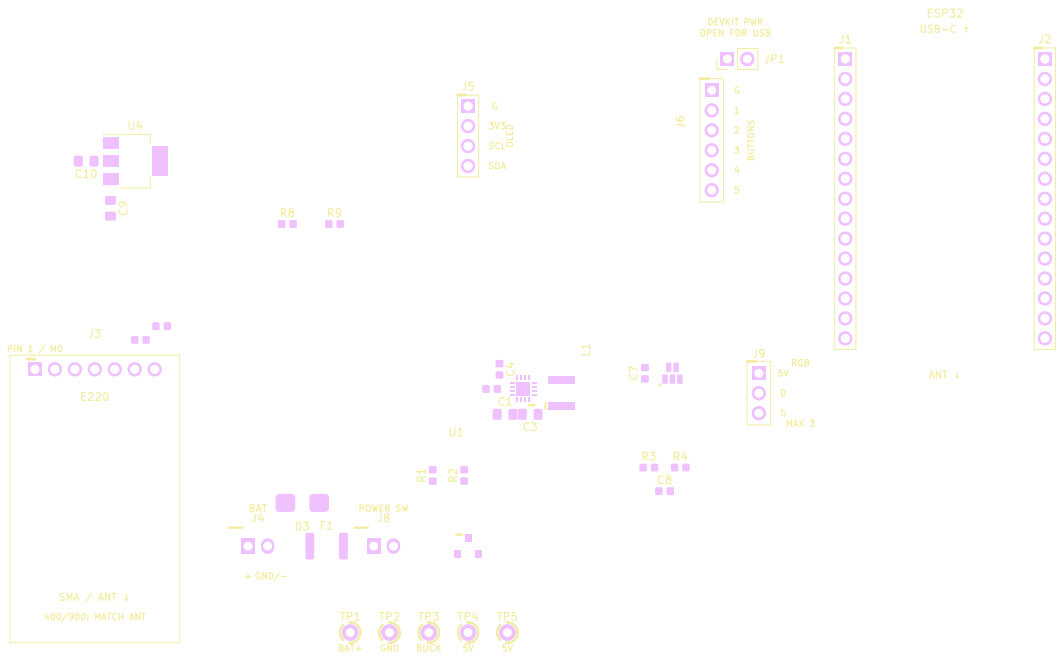
[picture p65: page 1]

DEVKIT PWR OPEN FOR USB OLED
