kvderevyanko/klicad/hardware/evidence/preexisting-esp32-e220-artifacts/samtec-ssw-s-review.pdf

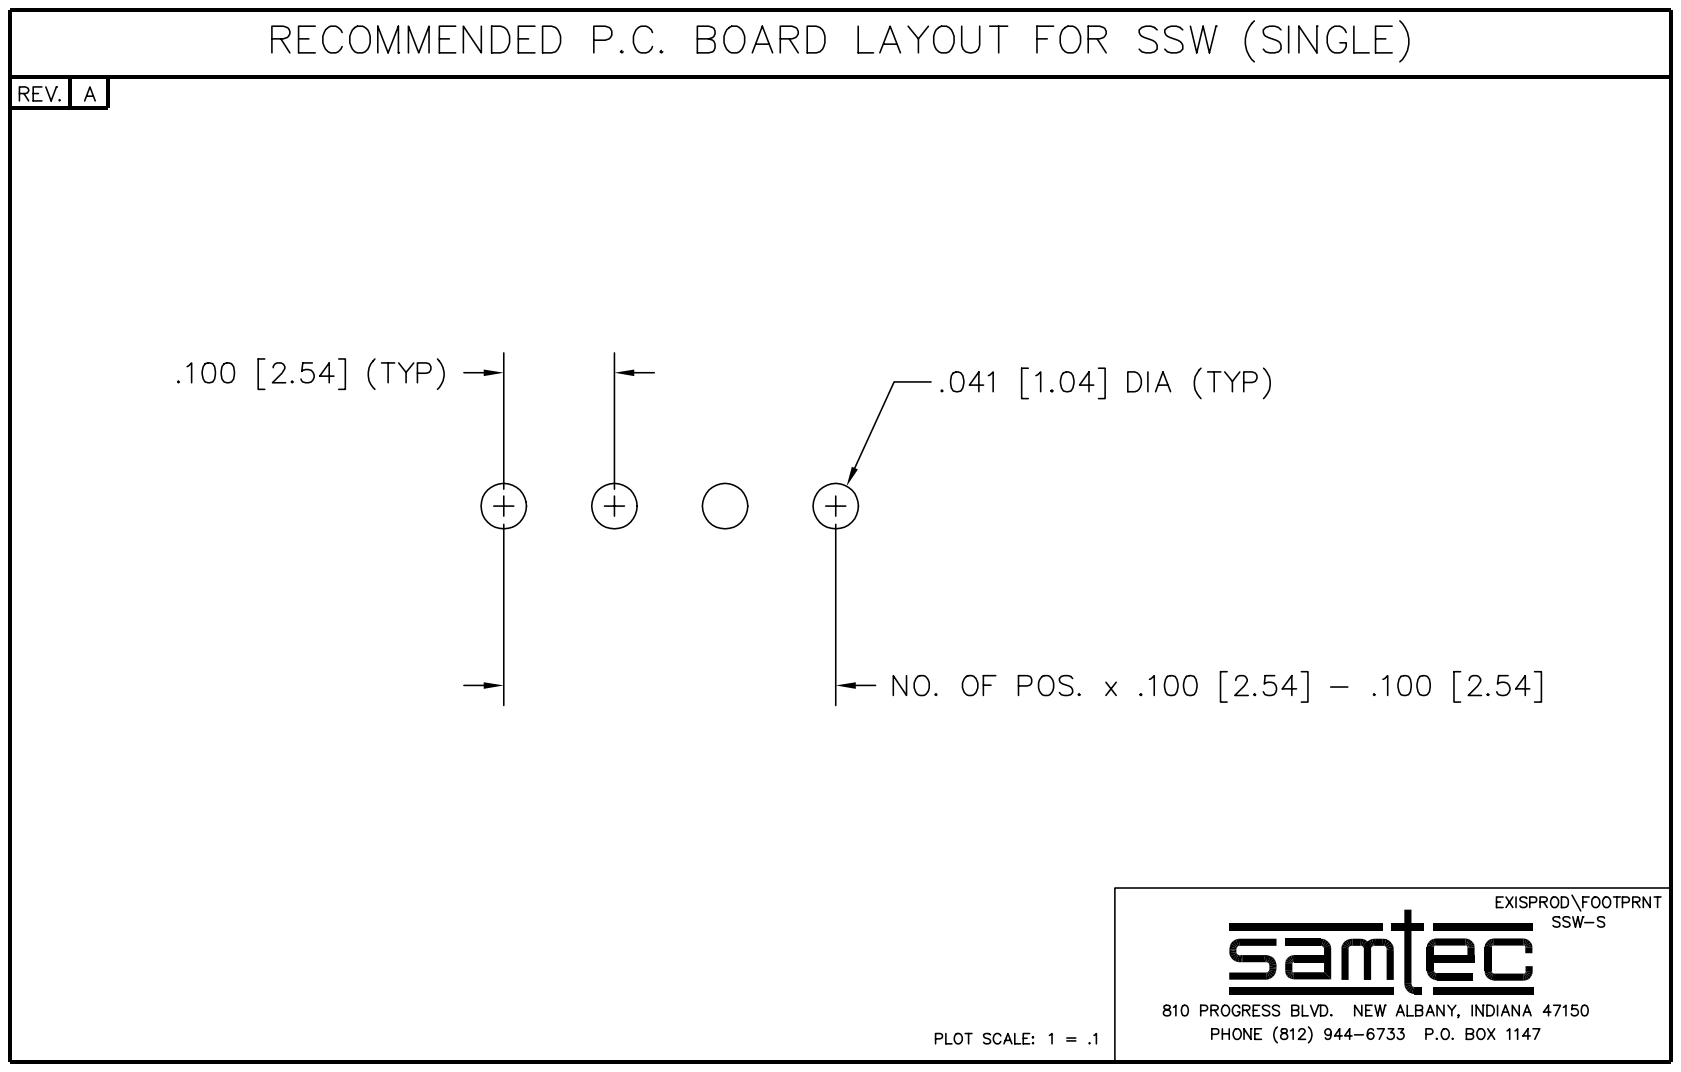
[picture p66: page 1]
