kvderevyanko/klicad/hardware/releases/rev1-q1-footprint-correction-2026-09-11/diagnostics/B_Cu_preview.pdf

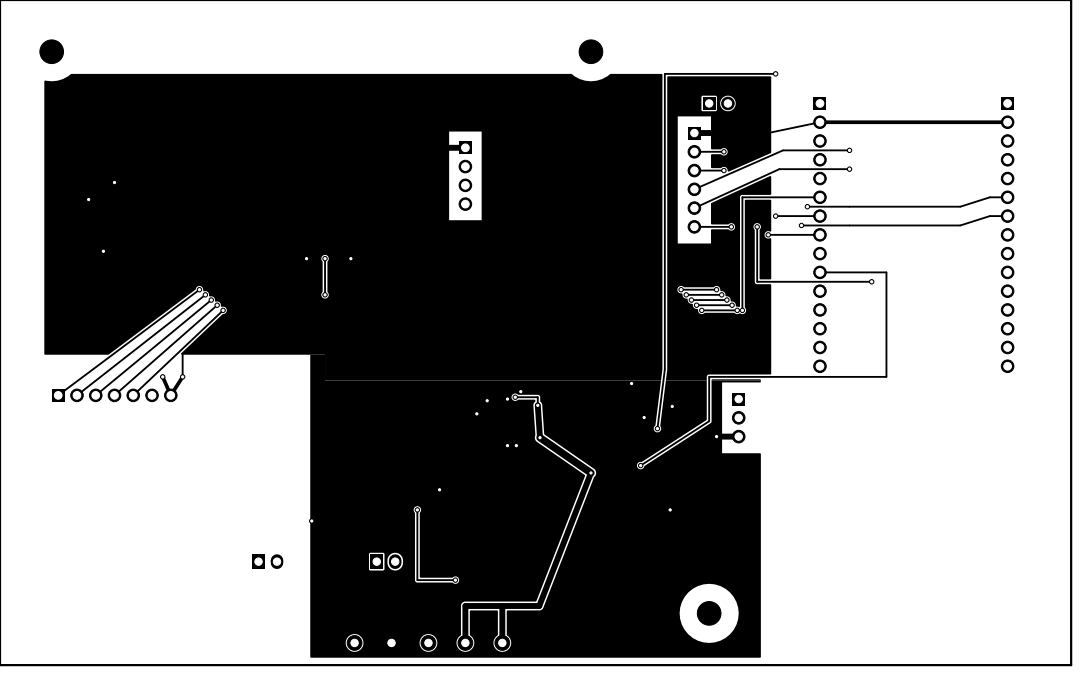
[picture p67: page 1]
