kvderevyanko/klicad/hardware/releases/rev1-q1-footprint-correction-2026-09-11/diagnostics/B_Mask_preview.pdf

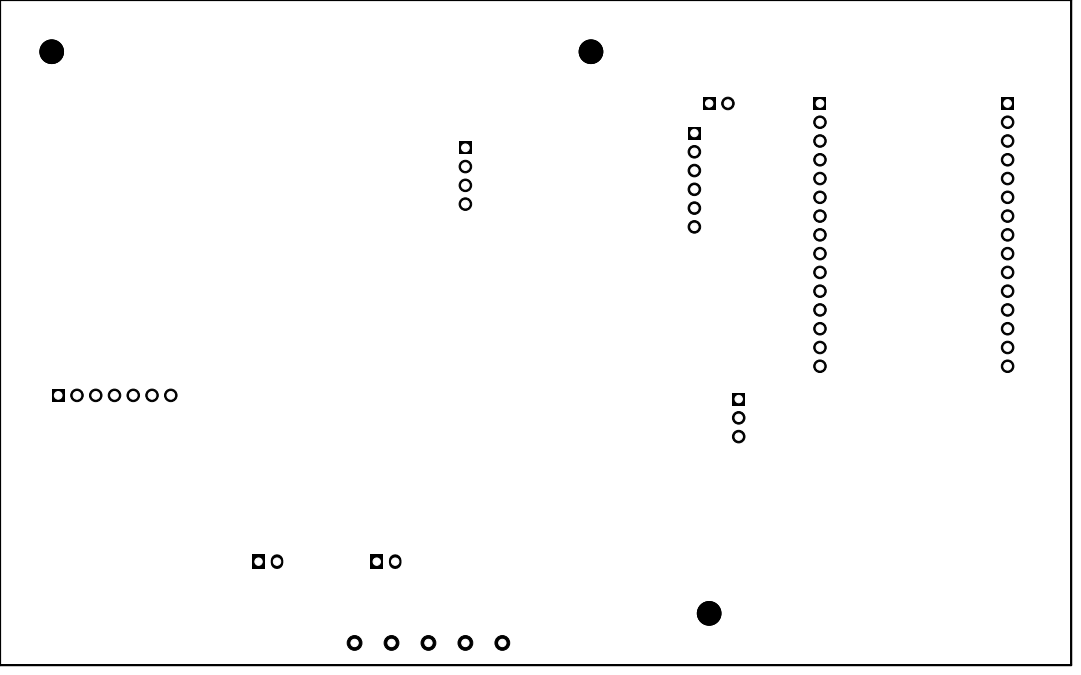
[picture p68: page 1]
