kvderevyanko/klicad/hardware/releases/rev1-q1-footprint-correction-2026-09-11/diagnostics/Drill_Map_PTH.pdf

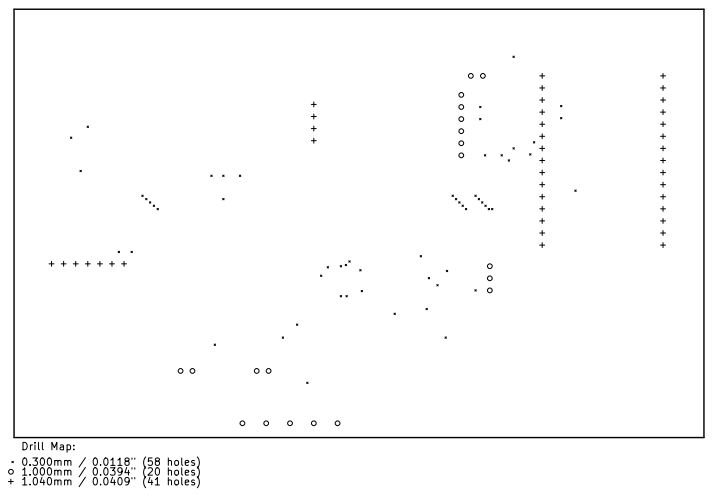
[picture p69: page 1]
