kvderevyanko/klicad/hardware/releases/rev1-q1-footprint-correction-2026-09-11/diagnostics/Edge_Cuts_preview.pdf

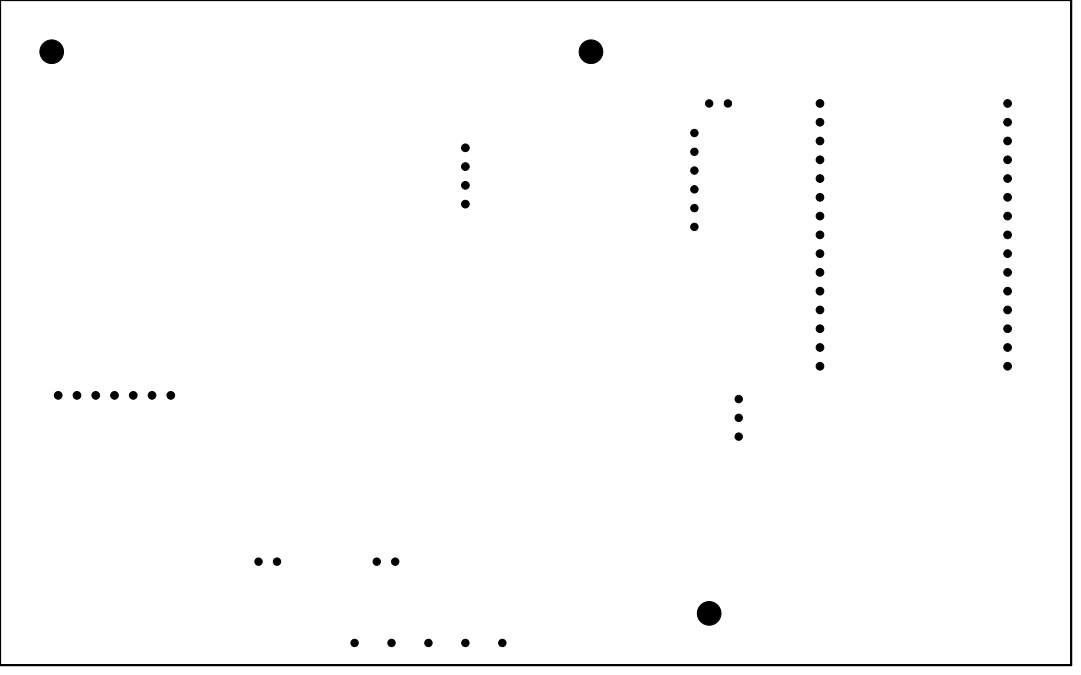
[picture p70: page 1]
