kvderevyanko/klicad/hardware/releases/rev1-q1-footprint-correction-2026-09-11/diagnostics/F_Cu_preview.pdf

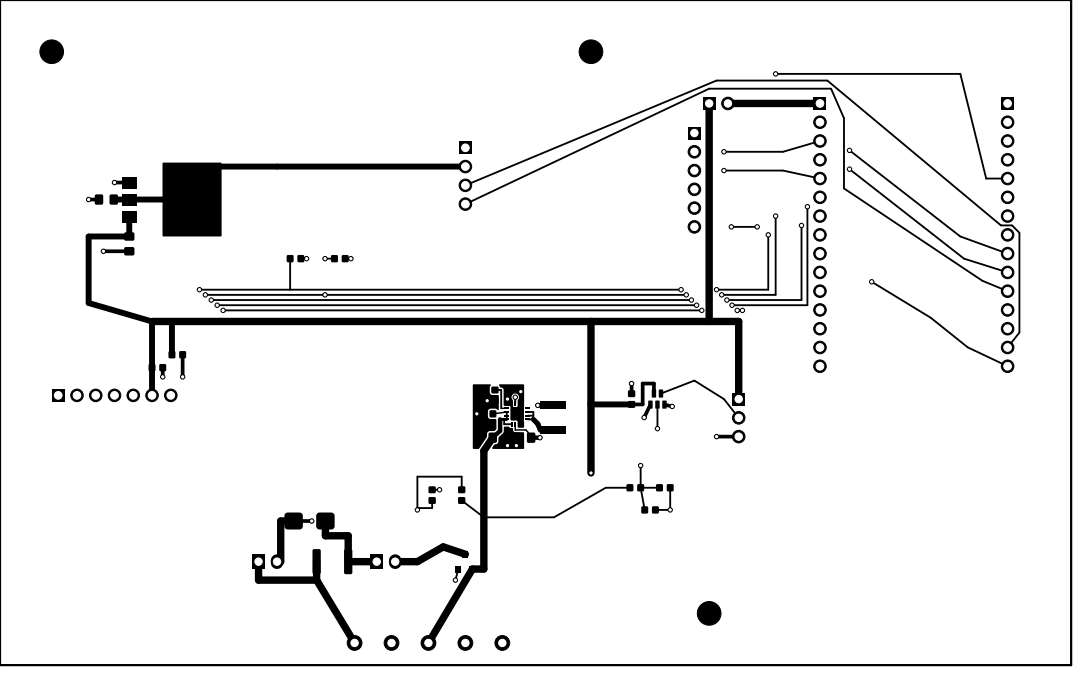
[picture p71: page 1]
