kvderevyanko/klicad/hardware/releases/rev1-q1-footprint-correction-2026-09-11/diagnostics/F_Mask_preview.pdf

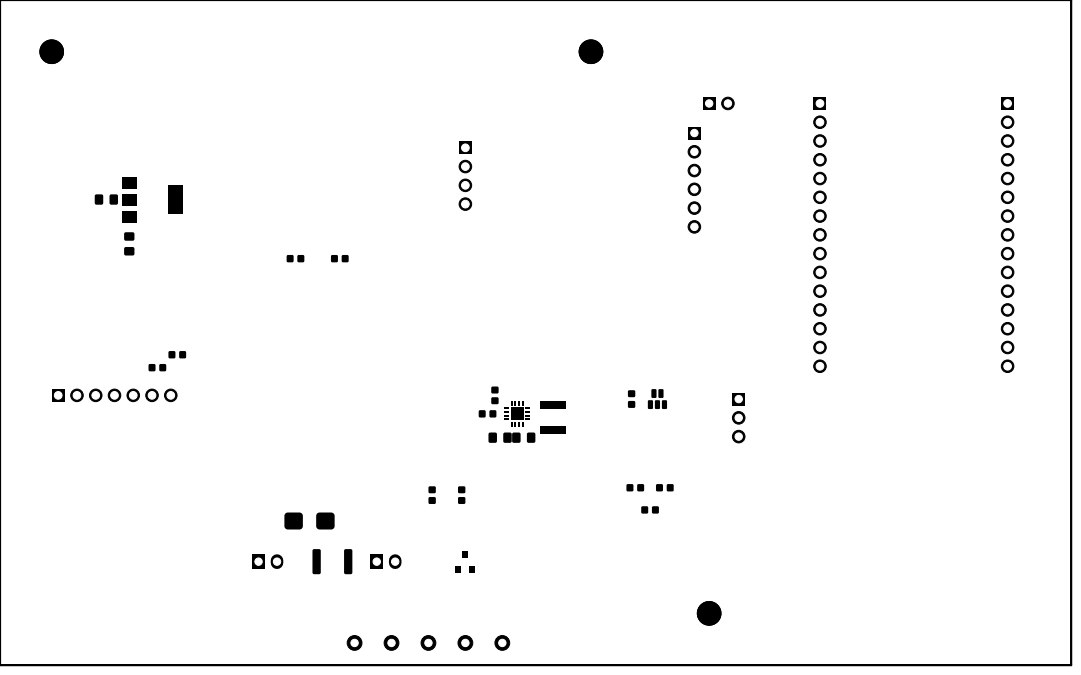
[picture p72: page 1]
