kvderevyanko/klicad/hardware/releases/rev1-q1-footprint-correction-2026-09-11/diagnostics/F_SilkS_preview.pdf

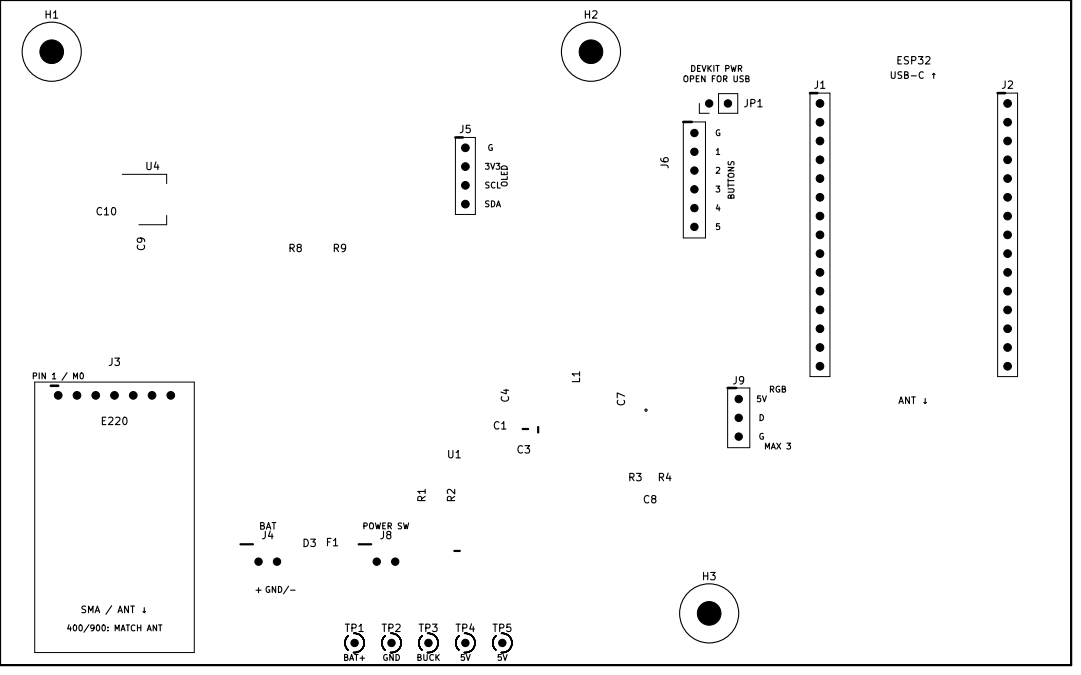
[picture p73: page 1]

DEVKIT PWR OPEN FOR USB
