kvderevyanko/klicad/hardware/releases/rev1-q1-footprint-correction-2026-09-11/documentation/silkscreen-top.pdf

DEVKIT PWR OPEN FOR USB
