kvderevyanko/klicad/hardware/releases/rev1/diagnostics/B_Cu_preview.pdf

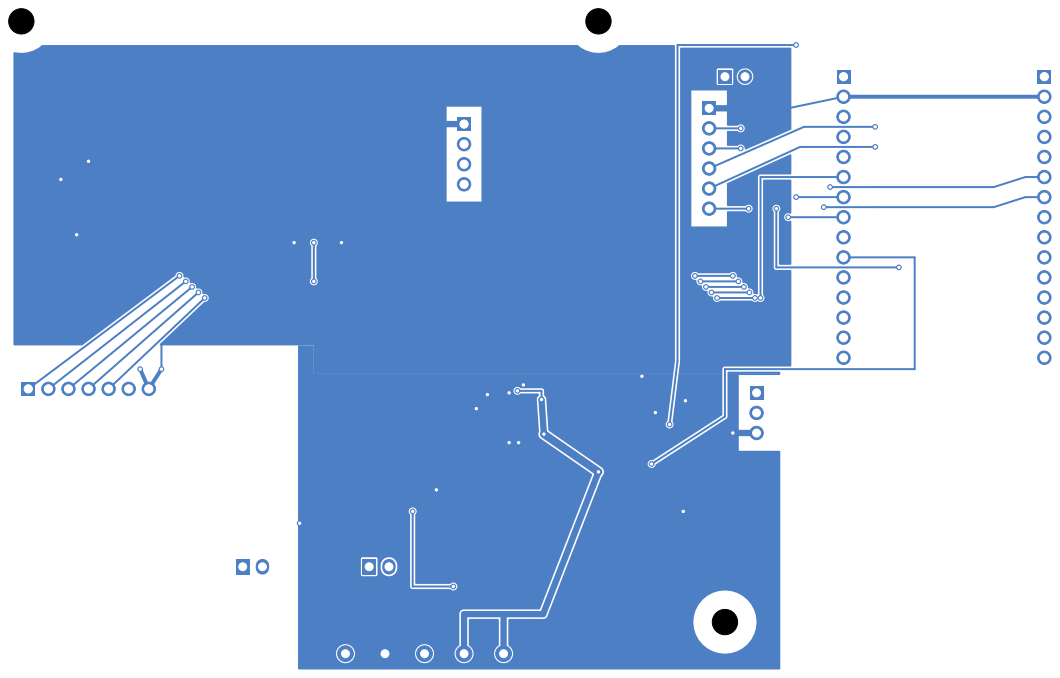
[picture p74: page 1]
