kvderevyanko/klicad/hardware/releases/rev1/diagnostics/B_Mask_preview.pdf

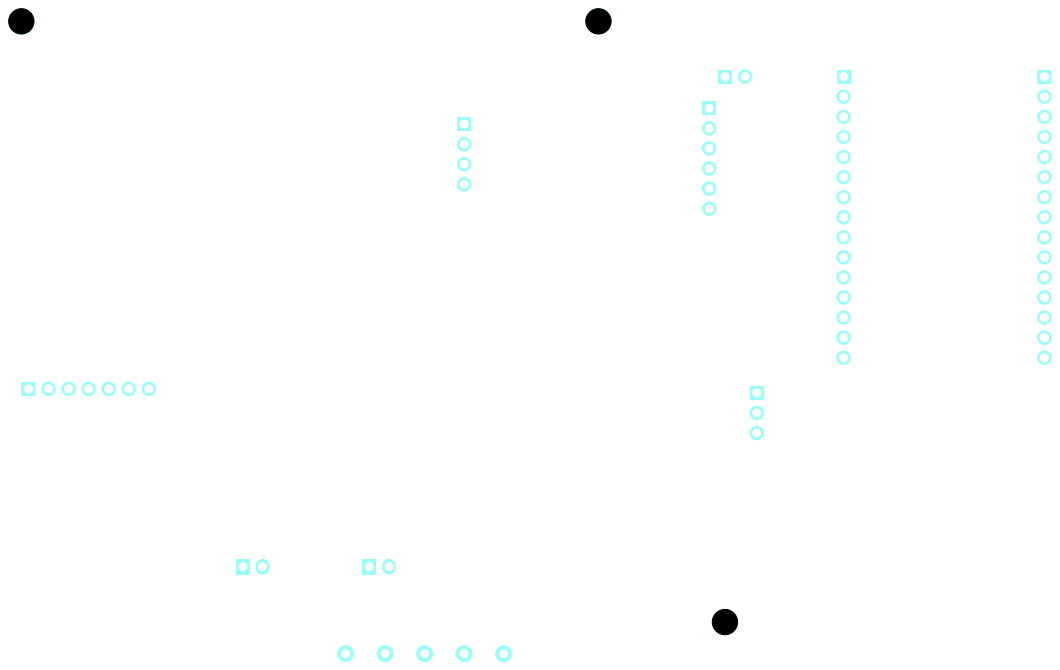
[picture p75: page 1]
