kvderevyanko/klicad/hardware/releases/rev1/diagnostics/Edge_Cuts_preview.pdf

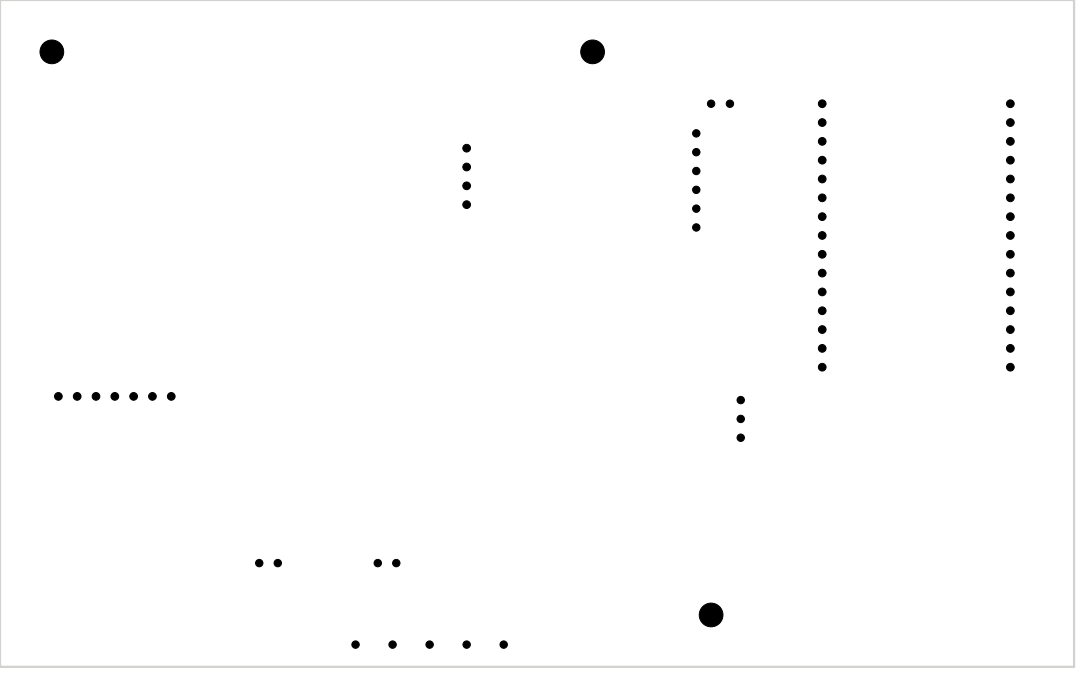
[picture p76: page 1]
