kvderevyanko/klicad/hardware/releases/rev1/diagnostics/F_Cu_preview.pdf

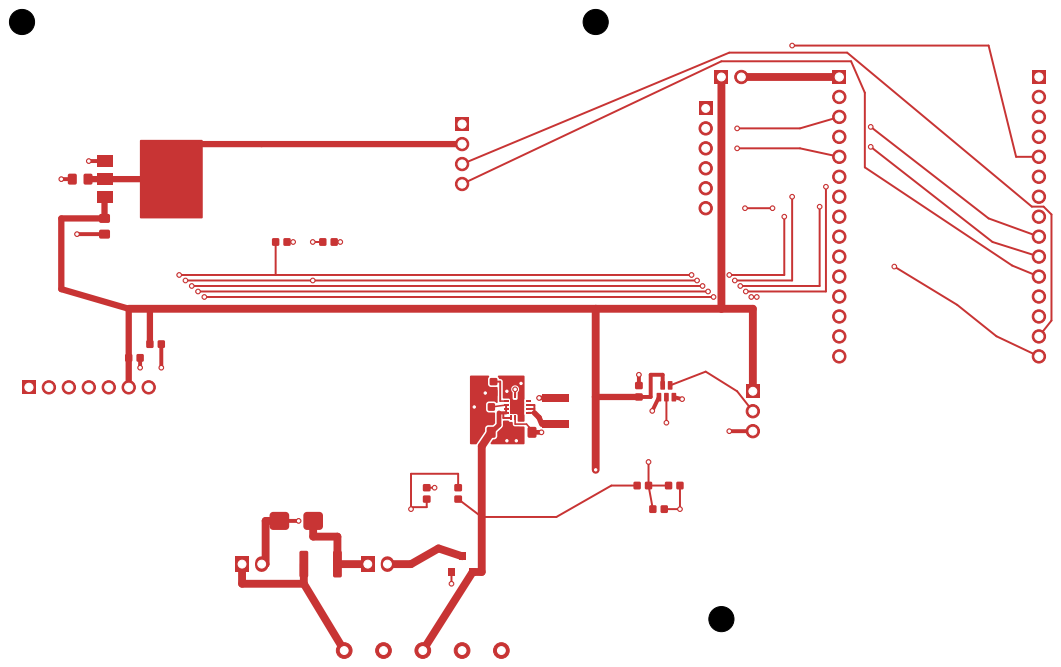
[picture p77: page 1]
