kvderevyanko/klicad/hardware/releases/rev1/diagnostics/F_Mask_preview.pdf

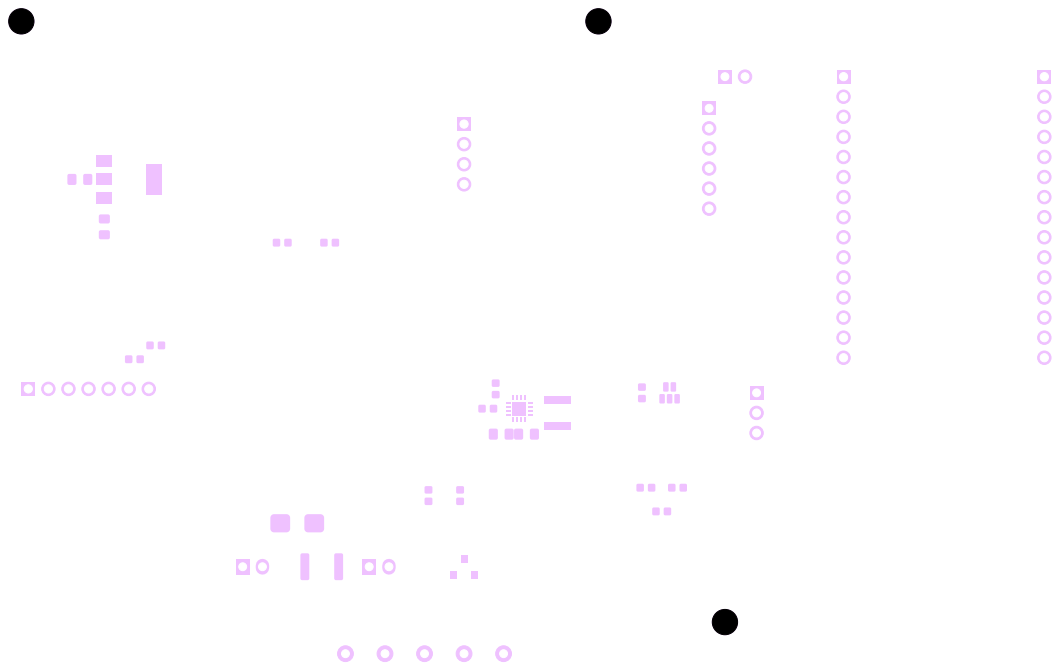
[picture p78: page 1]
