kvderevyanko/klicad/hardware/releases/rev1/diagnostics/F_SilkS_preview.pdf

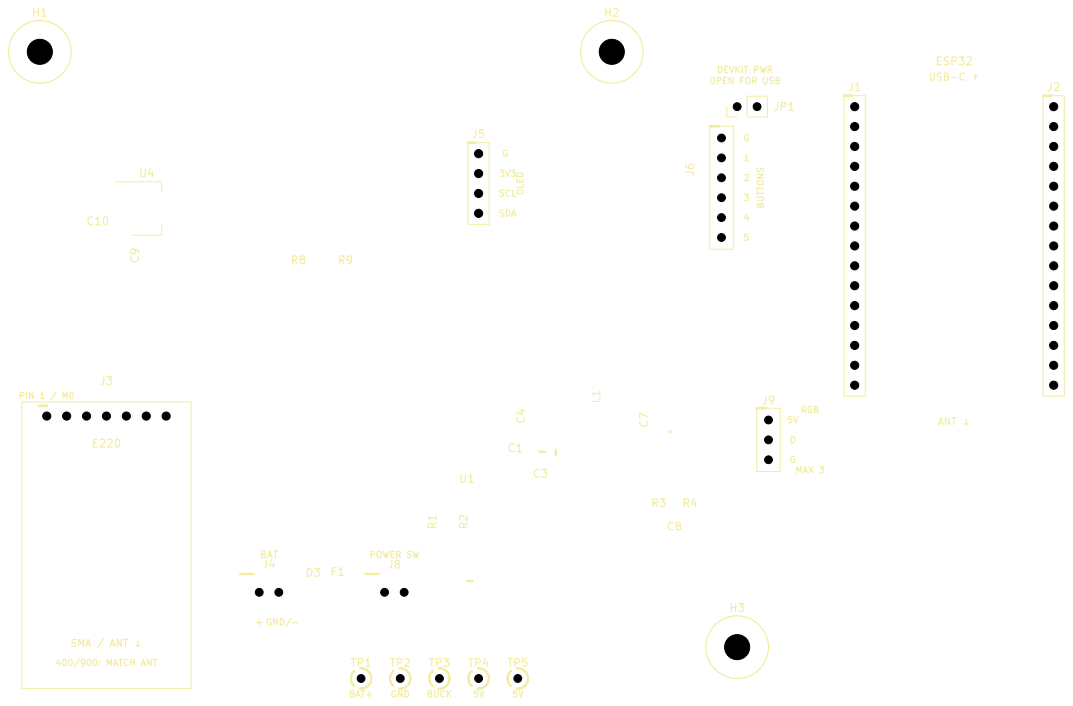
[picture p79: page 1]

DEVKIT PWR OPEN FOR USB
