kvderevyanko/klicad/hardware/evidence/rev1-physical-recovery-2026-08-20/j8-xh-electrical-source/esp32-e220.before-j8-xh.kicad_sch

## KiCad design hardware/evidence/rev1-physical-recovery-2026-08-20/j8-xh-electrical-source/esp32-e220.before-j8-xh.kicad_sch (2026-08-20)

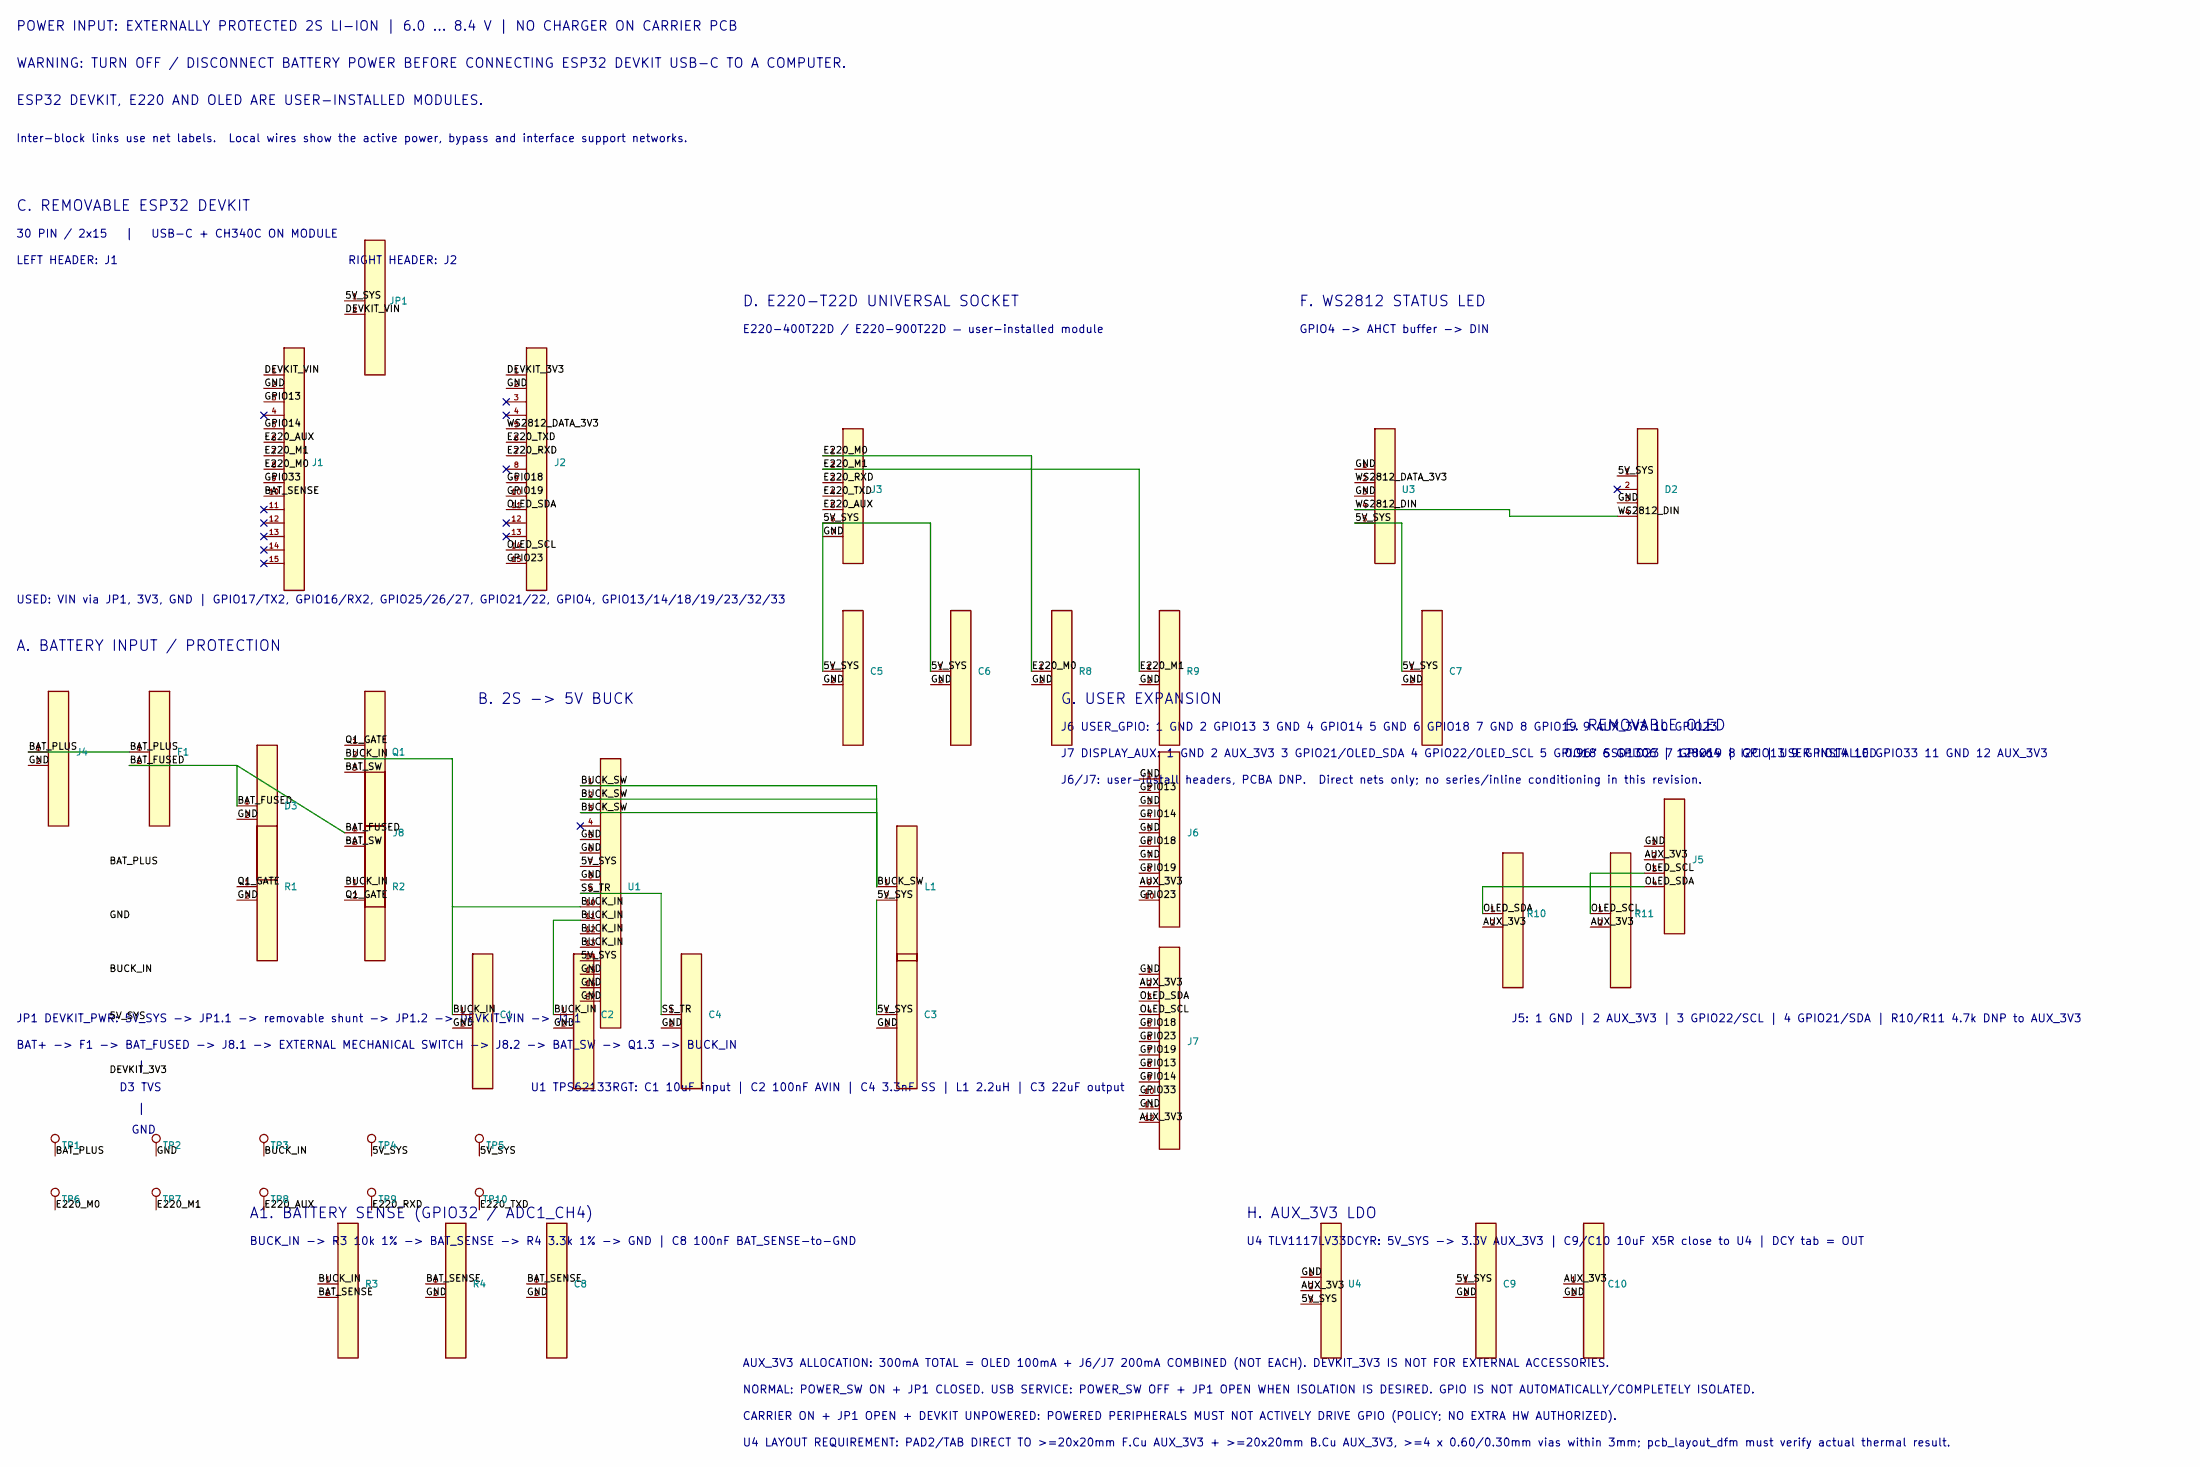
[picture p83: schematic esp32-e220.before-j8-xh.kicad_sch]

Parts:
C1, C9, C10: GRM21BR61E106KA73; Murata_GRM21_2012Metric
C2, C6, C7, C8: GRM188R71C104KA01D; Murata_GRM188_1608Metric
C3: GRM21BR61A226ME44; Murata_GRM21_2012Metric
C4: GRM1885C1H332JA01D; Murata_GRM188_1608Metric
C5: GRM188R61A106MAAL; Murata_GRM188_1608Metric
D2: WS2812B-V5; WorldSemi_WS2812B-V5_PLACEMENT_CANDIDATE_NOT_RELEASED
D3: SMBJ10CA; Littelfuse_SMBJ10CA_DO214AA
F1: 1812L200/16; Littelfuse_1812L200_16_4532Metric
J1: SSW-115-02-G-S DEVKIT LEFT; Samtec_SSW_1x15_P2.54mm_THT
J2: SSW-115-02-G-S DEVKIT RIGHT; Samtec_SSW_1x15_P2.54mm_THT
J3: E220-400T22D / E220-900T22D SOCKET; E220_T22D_Socket_400_900
J4: B2B-XH-A; JST_B2B-XH-A_1x02_P2.50mm_THT
J5: SSW-104-02-G-S; Samtec_SSW_1x04_P2.54mm_THT
J6: TSW-105-07-G-D; PinHeader_2x05_P2.54mm_Vertical
J7: TSW-106-07-G-D; PinHeader_2x06_P2.54mm_Vertical
J8: B2PS-VH(LF)(SN); JST_VH_B2PS-VH_1x02_P3.96mm_Horizontal
JP1: TSW-102-07-G-S + SNT-100-BK-G; PinHeader_1x02_P2.54mm_Vertical
L1: XFL4020-222MEB; Coilcraft_XFL4020-222MEB
Q1: DMP3130LQ-7; Diodes_DMP3130LQ-7_SOT23
R1: 100k 1%; Resistor_0603_1608Metric
R2: 1M 1%; Resistor_0603_1608Metric
R3: RC0603FR-0710KL; Resistor_0603_1608Metric
R4: RC0603FR-073K3L; Resistor_0603_1608Metric
R8, R9: 10k 1%; Resistor_0603_1608Metric
R10: DNP 4.7k 1% OLED SDA pull-up to AUX_3V3
R11: DNP 4.7k 1% OLED SCL pull-up to AUX_3V3
TP1: BAT_PLUS; TestPoint_THT_1p0mm_PROTOTYPE
TP2: GND; TestPoint_THT_1p0mm_PROTOTYPE
TP3: BUCK_IN; TestPoint_THT_1p0mm_PROTOTYPE
TP4, TP5: 5V_SYS; TestPoint_THT_1p0mm_PROTOTYPE
TP6: E220_M0; TestPoint_THT_1p0mm_PROTOTYPE
TP7: E220_M1; TestPoint_THT_1p0mm_PROTOTYPE
TP8: E220_AUX; TestPoint_THT_1p0mm_PROTOTYPE
TP9: E220_RXD; TestPoint_THT_1p0mm_PROTOTYPE
TP10: E220_TXD; TestPoint_THT_1p0mm_PROTOTYPE
U1: TPS62133RGT; TI_TPS62133RGT_RGT0016C
U3: SN74AHCT1G125DBVR; TI_SN74AHCT1G125DBVR_SOT23-5
U4: TLV1117LV33DCYR; SOT-223-3_TabPin2

Connections:
5V_SYS: C1.2, C2.2, C3.1, C3.2, C4.2, C5.1, C5.2, C6.1, C6.2, C7.1, C7.2, C8.2, C9.1, C9.2, C10.2, D2.1 (VDD), D2.3 (VSS), D3.2 (K), J1.2 (GND), J2.2 (GND), J3.6 (VCC), J3.7 (GND), J4.2 (BAT-), J5.1 (GND), J6.1 (GND), J6.3 (GND), J6.5 (GND), J6.7 (GND), J7.1 (GND), J7.11 (GND), JP1.1 (5V_SYS), L1.2, R1.2, R4.2, R8.2, R9.2, TP2.1, TP4.1, TP5.1, U1.5 (FB), U1.6 (AGND), U1.7 (FSW), U1.8 (DEF), U1.14 (VOS), U1.15 (PGND), U1.16 (PGND), U1.EP (EXPOSED THERMAL PAD), U3.1 (OE), U3.3 (GND), U3.5 (VCC), U4.1 (GND), U4.3 (IN)
AUX_3V3: C10.1, J5.2 (VCC / 3V3), J6.9 (AUX_3V3), J7.2 (AUX_3V3), J7.12 (AUX_3V3), R10.2, R11.2, U4.2 (OUT / TAB)
BAT_FUSED: D3.1 (A), F1.2, J8.1 (BAT_FUSED)
BAT_PLUS: F1.1, J4.1 (BAT+), TP1.1
BAT_SENSE: C8.1, J1.10 (GPIO32), R3.2, R4.1
BAT_SW: J8.2 (BAT_SW), Q1.3 (D)
BUCK_IN: C1.1, C2.1, Q1.2 (S), R2.1, R3.1, TP3.1, U1.10 (AVIN), U1.11 (PVIN), U1.12 (PVIN), U1.13 (EN)
BUCK_SW: L1.1, U1.1 (SW), U1.2 (SW), U1.3 (SW)
DEVKIT_3V3: J2.1 (3V3)
DEVKIT_VIN: J1.1 (VIN / 5V), JP1.2 (DEVKIT_VIN)
E220_AUX: J1.6 (GPIO27), J3.5 (AUX), TP8.1
E220_M0: J1.8 (GPIO25), J3.1 (M0), R8.1, TP6.1
E220_M1: J1.7 (GPIO26), J3.2 (M1), R9.1, TP7.1
E220_RXD: J2.7 (GPIO17/TX2), J3.3 (RXD), TP9.1
E220_TXD: J2.6 (GPIO16/RX2), J3.4 (TXD), TP10.1
GPIO13: J1.3 (GPIO13), J6.2 (GPIO13), J7.8 (GPIO13)
GPIO14: J1.5 (GPIO14), J6.4 (GPIO14), J7.9 (GPIO14)
GPIO18: J2.9 (GPIO18), J6.6 (GPIO18), J7.5 (GPIO18)
GPIO19: J2.10 (GPIO19), J6.8 (GPIO19), J7.7 (GPIO19)
GPIO23: J2.15 (GPIO23), J6.10 (GPIO23), J7.6 (GPIO23)
GPIO33: J1.9 (GPIO33), J7.10 (GPIO33)
OLED_SCL: J2.14 (GPIO22), J5.3 (SCL), J7.4 (GPIO22 / OLED_SCL), R11.1
OLED_SDA: J2.11 (GPIO21), J5.4 (SDA), J7.3 (GPIO21 / OLED_SDA), R10.1
Q1_GATE: Q1.1 (G), R1.1, R2.2
SS_TR: C4.1, U1.9 (SS/TR)
WS2812_DATA_3V3: J2.5 (GPIO4), U3.2 (A)
WS2812_DIN: D2.4 (DIN), U3.4 (Y)

Notes on the sheet:
A. BATTERY INPUT / PROTECTION
B. 2S -> 5V BUCK
H. AUX_3V3 LDO
U4 TLV1117LV33DCYR: 5V_SYS -> 3.3V AUX_3V3 | C9/C10 10uF X5R close to U4 | DCY tab = OUT
AUX_3V3 ALLOCATION: 300mA TOTAL = OLED 100mA + J6/J7 200mA COMBINED (NOT EACH). DEVKIT_3V3 IS NOT FOR EXTERNAL ACCESSORIES.
NORMAL: POWER_SW ON + JP1 CLOSED. USB SERVICE: POWER_SW OFF + JP1 OPEN WHEN ISOLATION IS DESIRED. GPIO IS NOT AUTOMATICALLY/COMPLETELY ISOLATED.
CARRIER ON + JP1 OPEN + DEVKIT UNPOWERED: POWERED PERIPHERALS MUST NOT ACTIVELY DRIVE GPIO (POLICY; NO EXTRA HW AUTHORIZED).
U4 LAYOUT REQUIREMENT: PAD2/TAB DIRECT TO >=20x20mm F.Cu AUX_3V3 + >=20x20mm B.Cu AUX_3V3, >=4 x 0.60/0.30mm vias within 3mm; pcb_layout_dfm must verify actual thermal result.
A1. BATTERY SENSE (GPIO32 / ADC1_CH4)
BUCK_IN -> R3 10k 1% -> BAT_SENSE -> R4 3.3k 1% -> GND | C8 100nF BAT_SENSE-to-GND
C. REMOVABLE ESP32 DEVKIT
30 PIN / 2x15 | USB-C + CH340C ON MODULE
LEFT HEADER: J1 RIGHT HEADER: J2
USED: VIN via JP1, 3V3, GND | GPIO17/TX2, GPIO16/RX2, GPIO25/26/27, GPIO21/22, GPIO4, GPIO13/14/18/19/23/32/33
D. E220-T22D UNIVERSAL SOCKET
E220-400T22D / E220-900T22D — user-installed module
F. WS2812 STATUS LED
GPIO4 -> AHCT buffer -> DIN
E. REMOVABLE OLED
0.96" SSD1306 | 128x64 | I2C | USER INSTALLED
POWER INPUT: EXTERNALLY PROTECTED 2S LI-ION | 6.0 ... 8.4 V | NO CHARGER ON CARRIER PCB
WARNING: TURN OFF / DISCONNECT BATTERY POWER BEFORE CONNECTING ESP32 DEVKIT USB-C TO A COMPUTER.
ESP32 DEVKIT, E220 AND OLED ARE USER-INSTALLED MODULES.
Inter-block links use net labels. Local wires show the active power, bypass and interface support networks.
G. USER EXPANSION
J6 USER_GPIO: 1 GND 2 GPIO13 3 GND 4 GPIO14 5 GND 6 GPIO18 7 GND 8 GPIO19 9 AUX_3V3 10 GPIO23
J7 DISPLAY_AUX: 1 GND 2 AUX_3V3 3 GPIO21/OLED_SDA 4 GPIO22/OLED_SCL 5 GPIO18 6 GPIO23 7 GPIO19 8 GPIO13 9 GPIO14 10 GPIO33 11 GND 12 AUX_3V3
J6/J7: user-install headers, PCBA DNP. Direct nets only; no series/inline conditioning in this revision.
JP1 DEVKIT_PWR: 5V_SYS -> JP1.1 -> removable shunt -> JP1.2 -> DEVKIT_VIN -> J1.1
BAT+ -> F1 -> BAT_FUSED -> J8.1 -> EXTERNAL MECHANICAL SWITCH -> J8.2 -> BAT_SW -> Q1.3 -> BUCK_IN
D3 TVS
GND
U1 TPS62133RGT: C1 10uF input | C2 100nF AVIN | C4 3.3nF SS | L1 2.2uH | C3 22uF output
J5: 1 GND | 2 AUX_3V3 | 3 GPIO22/SCL | 4 GPIO21/SDA | R10/R11 4.7k DNP to AUX_3V3
